eduardocasino/k-1008-visable-memory-card-replica/Address.kicad_sch

## KiCad design Address.kicad_sch (2023-08-17, an earlier design)

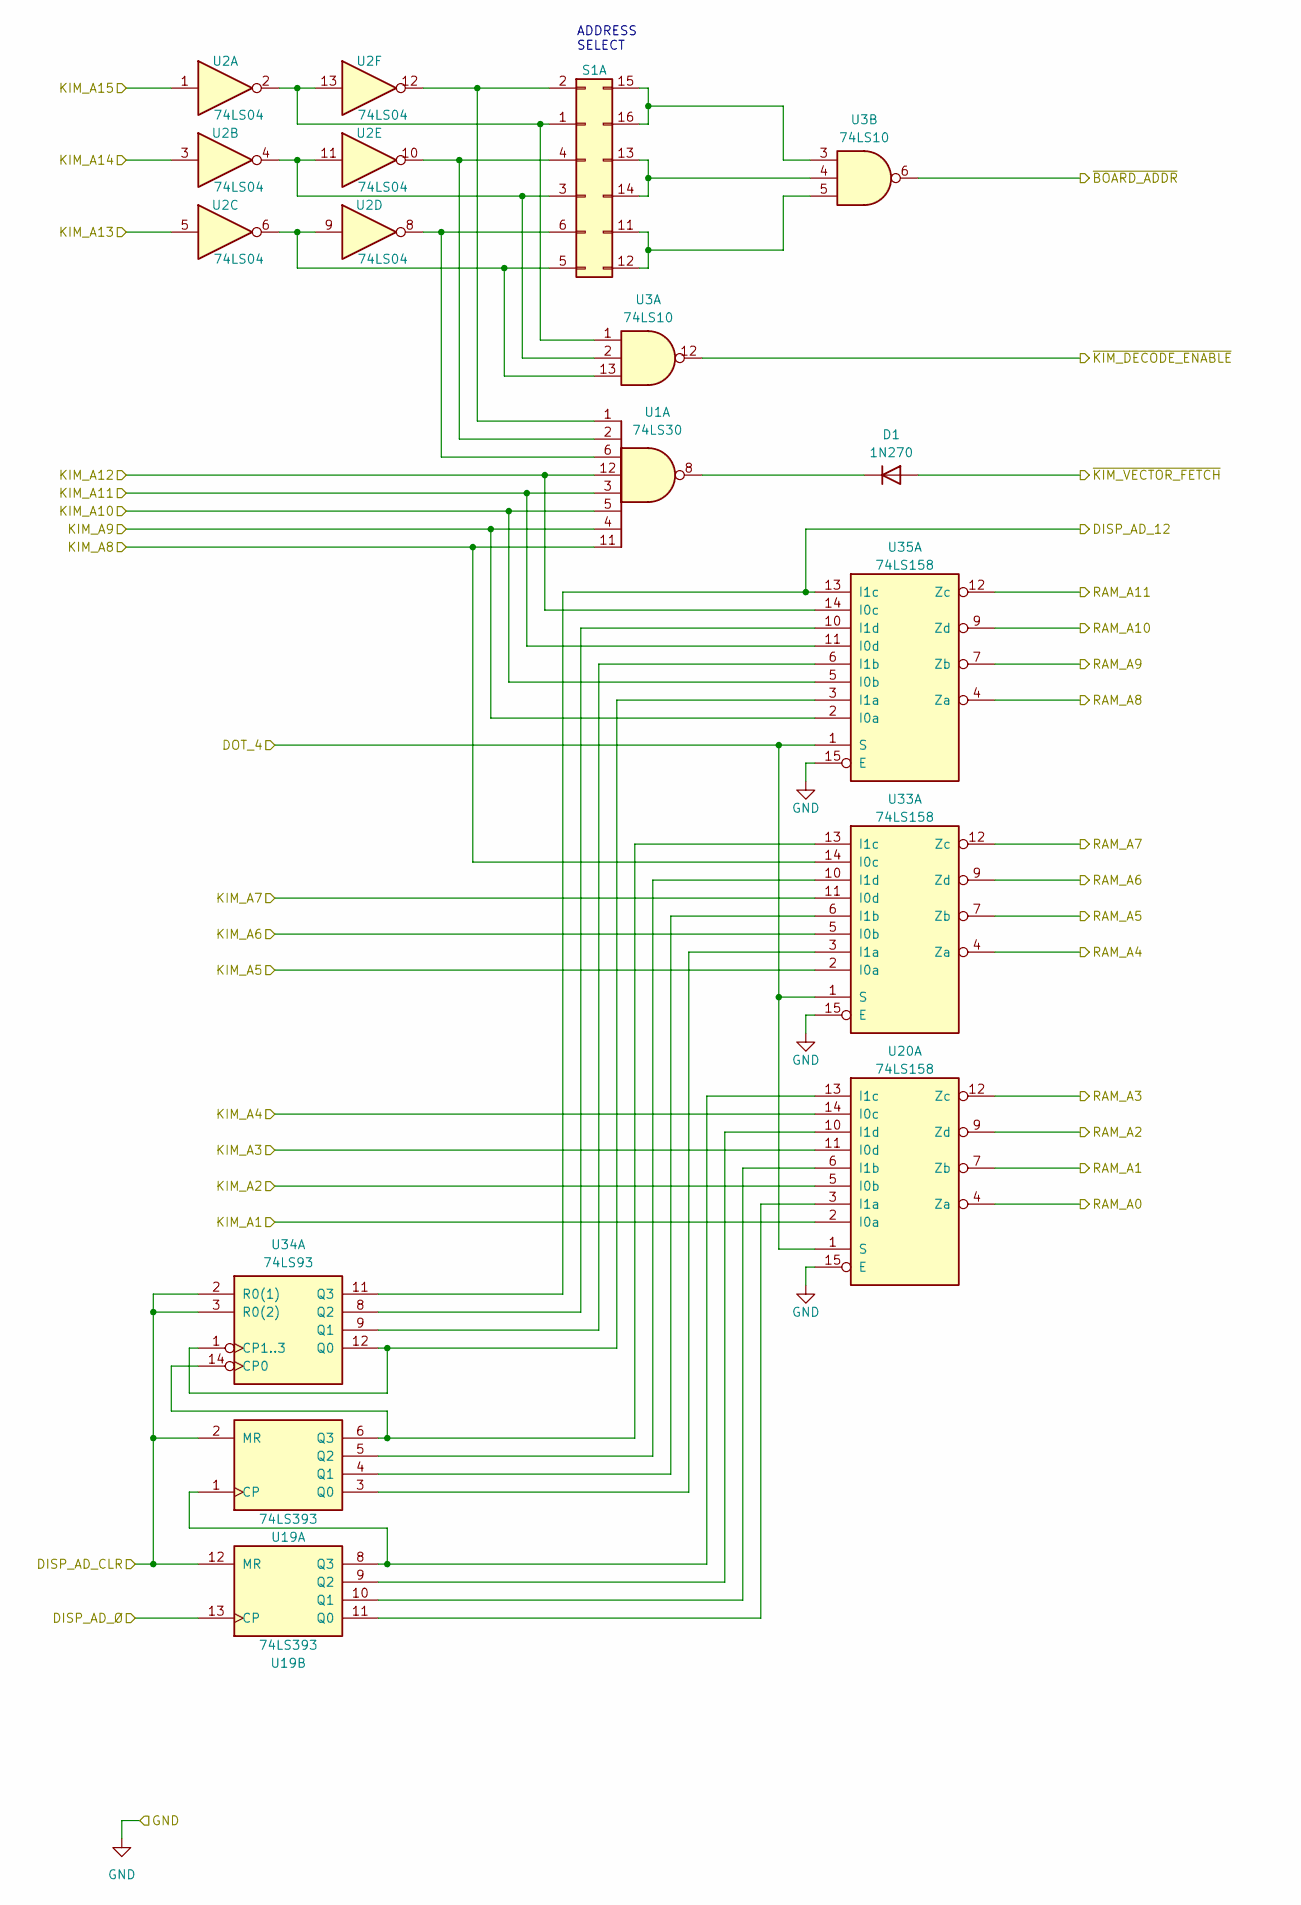
[picture p23: schematic Address.kicad_sch]

Parts:
D1: 1N270; D_DO-35_SOD27_P7.62mm_Horizontal
S1: DIP SOCKET FOR JUMPERS
U1: 74LS30
U2: 74LS04
U3: 74LS10
U19: 74LS393
U20, U33, U35: 74LS158
U34: 74LS93

Connections:
DISP_AD_12: U34.11 (Q3), U35.13 (I1c)
DISP_AD_CLR: U19.2 (MR), U19.12 (MR), U34.2 (R0(1)), U34.3 (R0(2))
DISP_AD_Ø: U19.13 (CP)
DOT_4: U20.1 (S), U33.1 (S), U35.1 (S)
GND: U20.15 (E), U33.15 (E), U35.15 (E)
KIM_A1: U20.2 (I0a)
KIM_A2: U20.5 (I0b)
KIM_A3: U20.11 (I0d)
KIM_A4: U20.14 (I0c)
KIM_A5: U33.2 (I0a)
KIM_A6: U33.5 (I0b)
KIM_A7: U33.11 (I0d)
KIM_A8: U1.11, U33.14 (I0c)
KIM_A9: U1.4, U35.2 (I0a)
KIM_A10: U1.5, U35.5 (I0b)
KIM_A11: U1.3, U35.11 (I0d)
KIM_A12: U1.12, U35.14 (I0c)
KIM_A13: U2.5
KIM_A14: U2.3
KIM_A15: U2.1
unnamed: D1.1 (K), U1.8
unnamed: S1.1, U2.2, U2.13, U3.1
unnamed: S1.2, U1.1, U2.12
unnamed: S1.3, U2.4, U2.11, U3.2
unnamed: S1.4, U1.2, U2.10
unnamed: S1.5, U2.6, U2.9, U3.13
unnamed: S1.6, U1.6, U2.8
unnamed: S1.11, S1.12, U3.5
unnamed: S1.13, S1.14, U3.4
unnamed: S1.15, S1.16, U3.3
unnamed: U19.1 (CP), U19.8 (Q3), U20.13 (I1c)
unnamed: U19.3 (Q0), U33.3 (I1a)
unnamed: U19.4 (Q1), U33.6 (I1b)
unnamed: U19.5 (Q2), U33.10 (I1d)
unnamed: U19.6 (Q3), U33.13 (I1c), U34.14 (CP0)
unnamed: U19.9 (Q2), U20.10 (I1d)
unnamed: U19.10 (Q1), U20.6 (I1b)
unnamed: U19.11 (Q0), U20.3 (I1a)
unnamed: U34.1 (CP1..3), U34.12 (Q0), U35.3 (I1a)
unnamed: U34.8 (Q2), U35.10 (I1d)
unnamed: U34.9 (Q1), U35.6 (I1b)
RAM_A0: U20.4 (Za)
RAM_A1: U20.7 (Zb)
RAM_A2: U20.9 (Zd)
RAM_A3: U20.12 (Zc)
RAM_A4: U33.4 (Za)
RAM_A5: U33.7 (Zb)
RAM_A6: U33.9 (Zd)
RAM_A7: U33.12 (Zc)
RAM_A8: U35.4 (Za)
RAM_A9: U35.7 (Zb)
RAM_A10: U35.9 (Zd)
RAM_A11: U35.12 (Zc)
~BOARD_ADDR: U3.6
~KIM_DECODE_ENABLE: U3.12
~KIM_VECTOR_FETCH: D1.2 (A)

Notes on the sheet:
ADDRESS SELECT
