eduardocasino/k-1008-visable-memory-card-replica/Power_pins_and_decoupling_caps.kicad_sch

## KiCad design Power_pins_and_decoupling_caps.kicad_sch (2023-08-17, an earlier design)

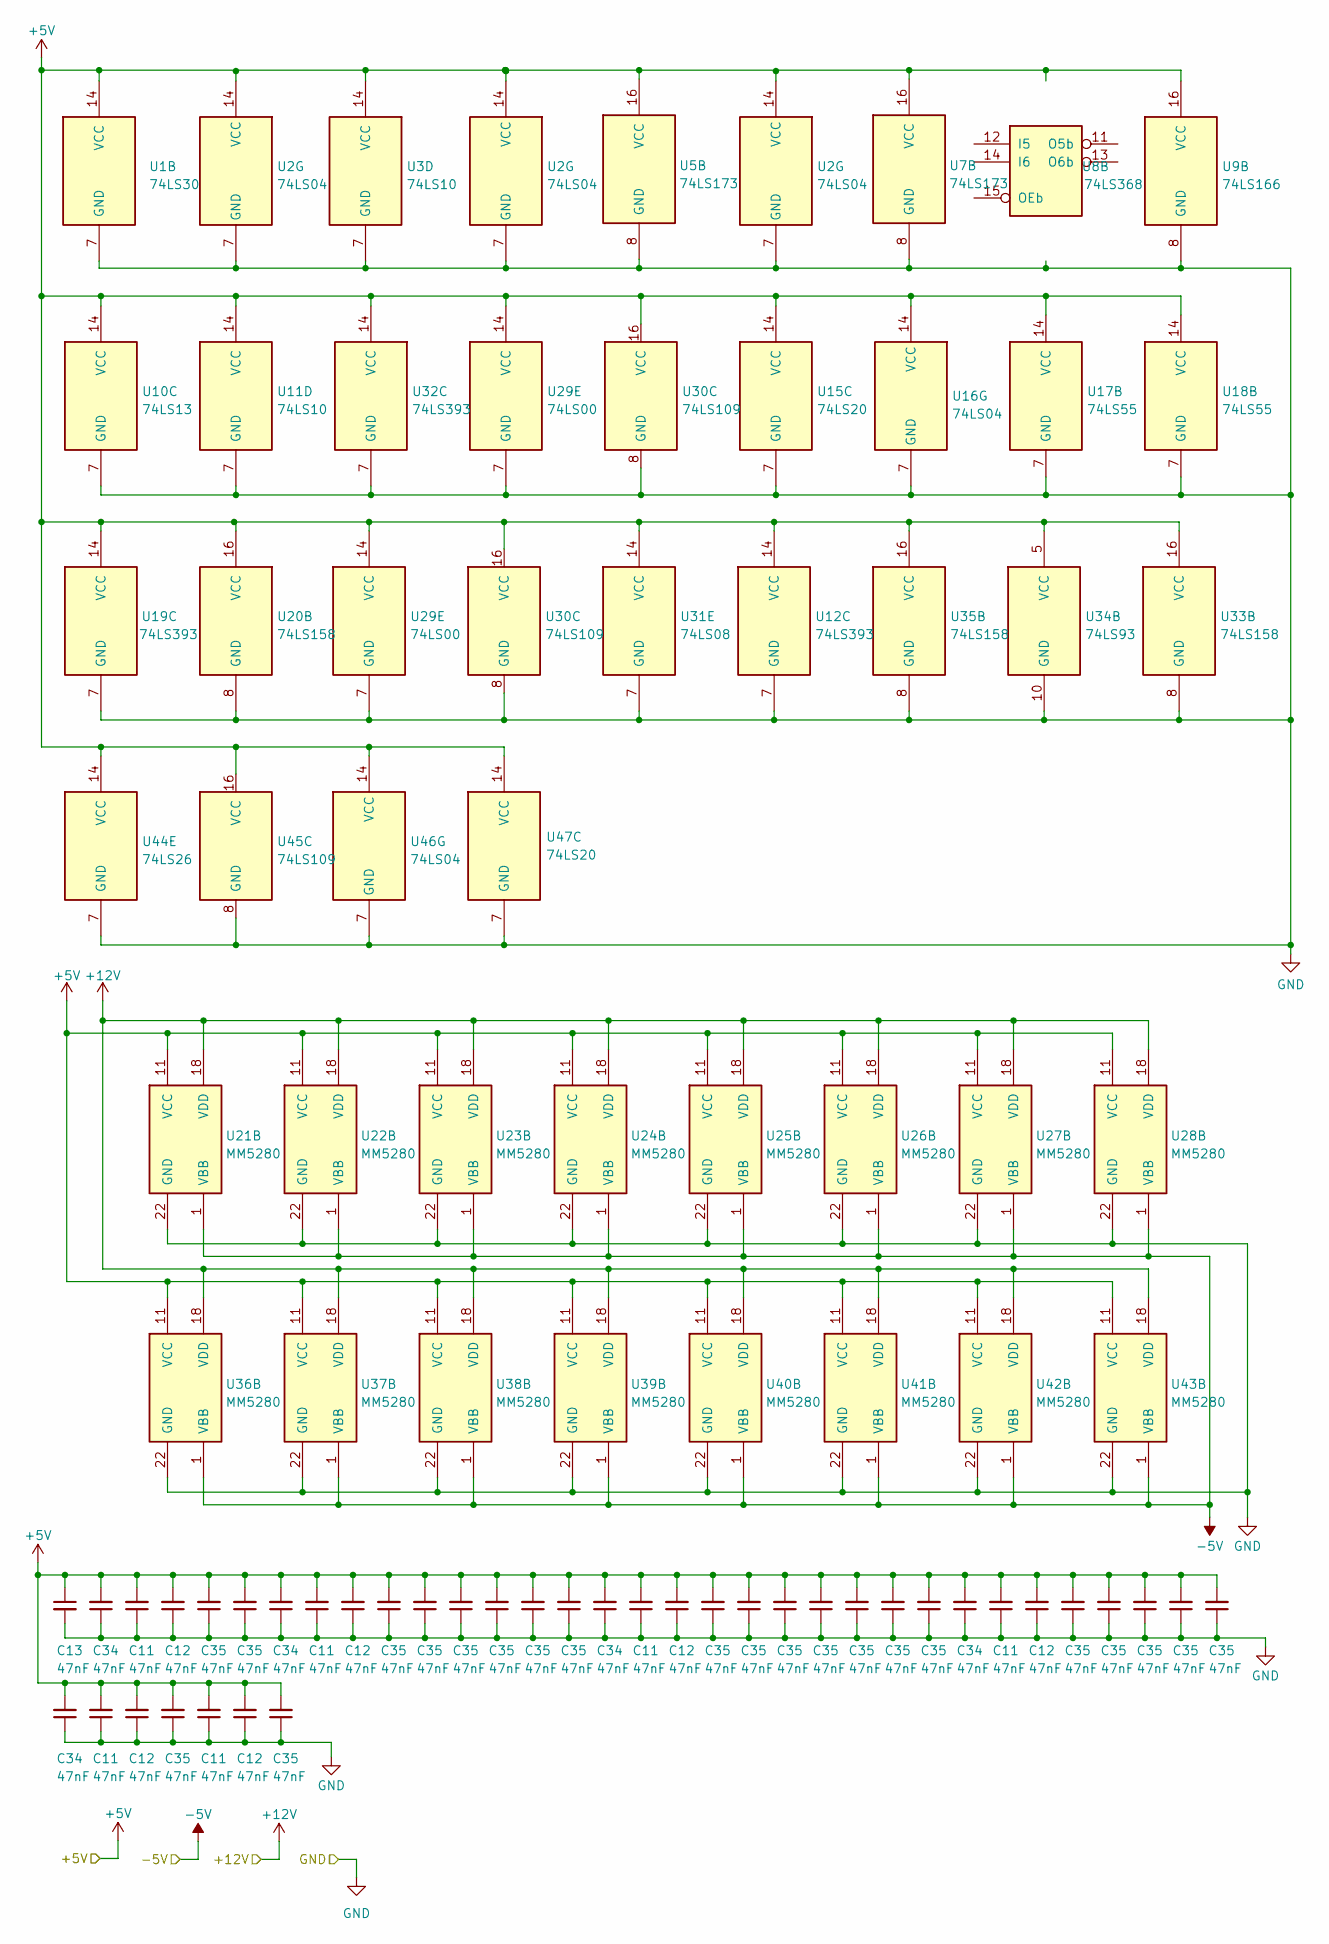
[picture p24: schematic Power_pins_and_decoupling_caps.kicad_sch]

Parts:
C11, C12, C13, C34, C35: 47nF
U1: 74LS30
U2, U16, U46: 74LS04
U3, U11: 74LS10
U5, U7: 74LS173
U8: 74LS368
U9: 74LS166
U10: 74LS13
U12, U19, U32: 74LS393
U15, U47: 74LS20
U17, U18: 74LS55
U20, U33, U35: 74LS158
U21, U22, U23, U24, U25, U26, U27, U28, U36, U37, U38, U39, U40, U41, U42, U43: MM5280
U29: 74LS00
U30, U45: 74LS109
U31: 74LS08
U34: 74LS93
U44: 74LS26

Connections:
+5V: C11.2, C12.2, C13.1, C34.2, C35.2, U1.14 (VCC), U2.14 (VCC), U3.14 (VCC), U5.16 (VCC), U7.16 (VCC), U9.16 (VCC), U10.14 (VCC), U11.14 (VCC), U12.14 (VCC), U15.14 (VCC), U16.14 (VCC), U17.14 (VCC), U18.14 (VCC), U19.14 (VCC), U20.16 (VCC), U21.11 (VCC), U22.11 (VCC), U23.11 (VCC), U24.11 (VCC), U25.11 (VCC), U26.11 (VCC), U27.11 (VCC), U28.11 (VCC), U29.14 (VCC), U30.16 (VCC), U31.14 (VCC), U32.14 (VCC), U33.16 (VCC), U34.5 (VCC), U35.16 (VCC), U36.11 (VCC), U37.11 (VCC), U38.11 (VCC), U39.11 (VCC), U40.11 (VCC), U41.11 (VCC), U42.11 (VCC), U43.11 (VCC), U44.14 (VCC), U45.16 (VCC), U46.14 (VCC), U47.14 (VCC)
+12V: U21.18 (VDD), U22.18 (VDD), U23.18 (VDD), U24.18 (VDD), U25.18 (VDD), U26.18 (VDD), U27.18 (VDD), U28.18 (VDD), U36.18 (VDD), U37.18 (VDD), U38.18 (VDD), U39.18 (VDD), U40.18 (VDD), U41.18 (VDD), U42.18 (VDD), U43.18 (VDD)
-5V: U21.1 (VBB), U22.1 (VBB), U23.1 (VBB), U24.1 (VBB), U25.1 (VBB), U26.1 (VBB), U27.1 (VBB), U28.1 (VBB), U36.1 (VBB), U37.1 (VBB), U38.1 (VBB), U39.1 (VBB), U40.1 (VBB), U41.1 (VBB), U42.1 (VBB), U43.1 (VBB)
GND: C11.1, C12.1, C13.2, C34.1, C35.1, U1.7 (GND), U2.7 (GND), U3.7 (GND), U5.8 (GND), U7.8 (GND), U9.8 (GND), U10.7 (GND), U11.7 (GND), U12.7 (GND), U15.7 (GND), U16.7 (GND), U17.7 (GND), U18.7 (GND), U19.7 (GND), U20.8 (GND), U21.22 (GND), U22.22 (GND), U23.22 (GND), U24.22 (GND), U25.22 (GND), U26.22 (GND), U27.22 (GND), U28.22 (GND), U29.7 (GND), U30.8 (GND), U31.7 (GND), U32.7 (GND), U33.8 (GND), U34.10 (GND), U35.8 (GND), U36.22 (GND), U37.22 (GND), U38.22 (GND), U39.22 (GND), U40.22 (GND), U41.22 (GND), U42.22 (GND), U43.22 (GND), U44.7 (GND), U45.8 (GND), U46.7 (GND), U47.7 (GND)
