eduardocasino/k-1008-visable-memory-card-replica/Ram_chips_high.kicad_sch

## KiCad design Ram_chips_high.kicad_sch (2023-07-14, an earlier design)

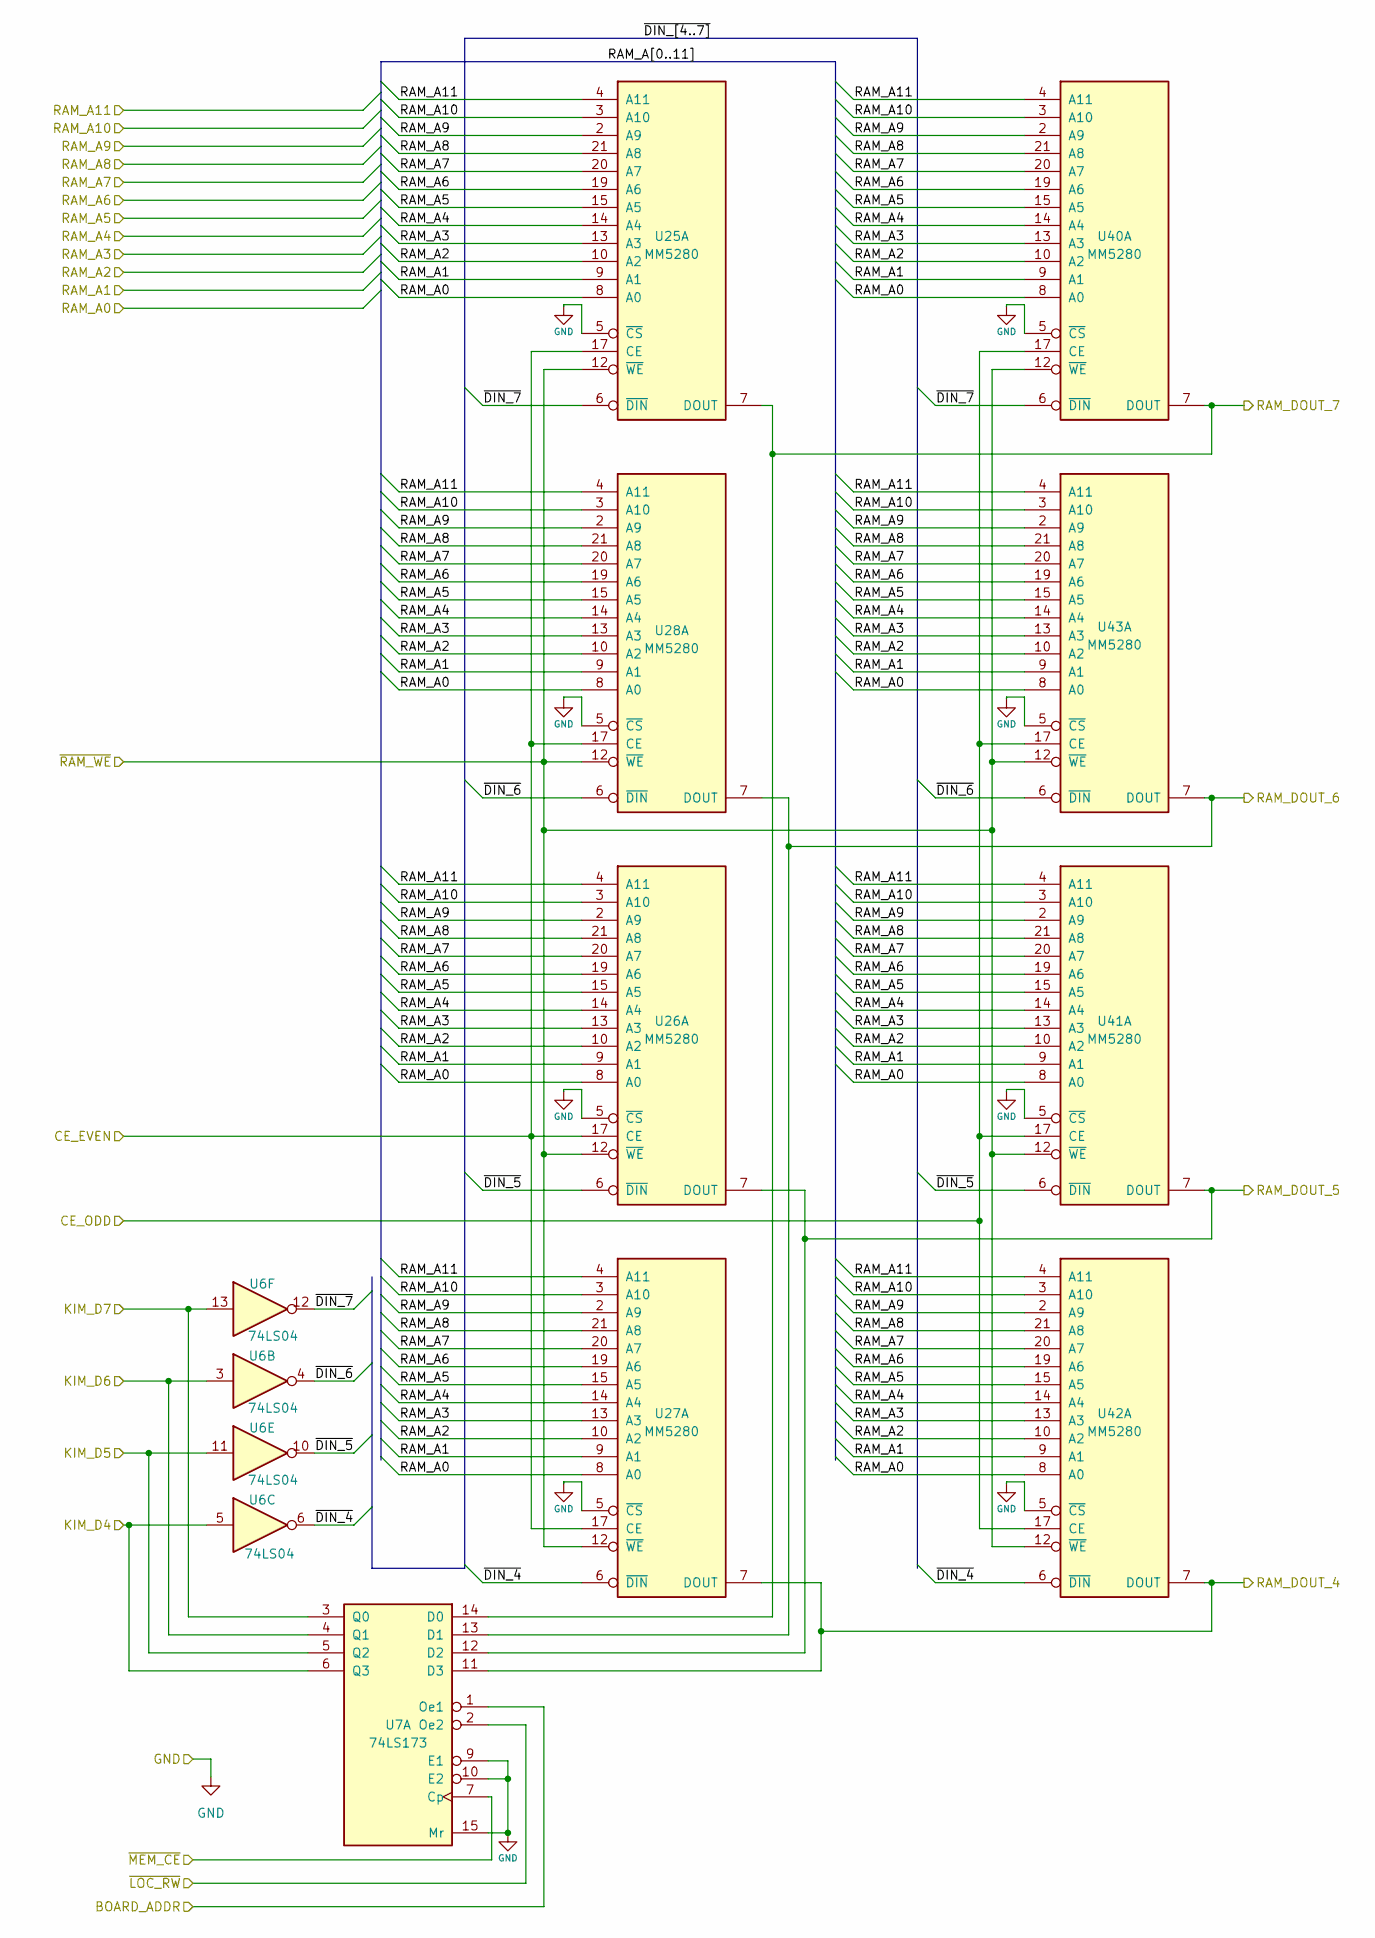
[picture p25: schematic Ram_chips_high.kicad_sch]

Parts:
U6: 74LS04
U7: 74LS173
U25, U26, U27, U28, U40, U41, U42, U43: MM5280

Connections:
BOARD_ADDR: U7.1 (Oe1)
CE_EVEN: U25.17 (CE), U26.17 (CE), U27.17 (CE), U28.17 (CE)
CE_ODD: U40.17 (CE), U41.17 (CE), U42.17 (CE), U43.17 (CE)
GND: U7.9 (E1), U7.10 (E2), U7.15 (Mr), U25.5 (~CS), U26.5 (~CS), U27.5 (~CS), U28.5 (~CS), U40.5 (~CS), U41.5 (~CS), U42.5 (~CS), U43.5 (~CS)
KIM_D4: U6.5, U7.6 (Q3)
KIM_D5: U6.11, U7.5 (Q2)
KIM_D6: U6.3, U7.4 (Q1)
KIM_D7: U6.13, U7.3 (Q0)
RAM_A0: U25.8 (A0), U26.8 (A0), U27.8 (A0), U28.8 (A0), U40.8 (A0), U41.8 (A0), U42.8 (A0), U43.8 (A0)
RAM_A1: U25.9 (A1), U26.9 (A1), U27.9 (A1), U28.9 (A1), U40.9 (A1), U41.9 (A1), U42.9 (A1), U43.9 (A1)
RAM_A2: U25.10 (A2), U26.10 (A2), U27.10 (A2), U28.10 (A2), U40.10 (A2), U41.10 (A2), U42.10 (A2), U43.10 (A2)
RAM_A3: U25.13 (A3), U26.13 (A3), U27.13 (A3), U28.13 (A3), U40.13 (A3), U41.13 (A3), U42.13 (A3), U43.13 (A3)
RAM_A4: U25.14 (A4), U26.14 (A4), U27.14 (A4), U28.14 (A4), U40.14 (A4), U41.14 (A4), U42.14 (A4), U43.14 (A4)
RAM_A5: U25.15 (A5), U26.15 (A5), U27.15 (A5), U28.15 (A5), U40.15 (A5), U41.15 (A5), U42.15 (A5), U43.15 (A5)
RAM_A6: U25.19 (A6), U26.19 (A6), U27.19 (A6), U28.19 (A6), U40.19 (A6), U41.19 (A6), U42.19 (A6), U43.19 (A6)
RAM_A7: U25.20 (A7), U26.20 (A7), U27.20 (A7), U28.20 (A7), U40.20 (A7), U41.20 (A7), U42.20 (A7), U43.20 (A7)
RAM_A8: U25.21 (A8), U26.21 (A8), U27.21 (A8), U28.21 (A8), U40.21 (A8), U41.21 (A8), U42.21 (A8), U43.21 (A8)
RAM_A9: U25.2 (A9), U26.2 (A9), U27.2 (A9), U28.2 (A9), U40.2 (A9), U41.2 (A9), U42.2 (A9), U43.2 (A9)
RAM_A10: U25.3 (A10), U26.3 (A10), U27.3 (A10), U28.3 (A10), U40.3 (A10), U41.3 (A10), U42.3 (A10), U43.3 (A10)
RAM_A11: U25.4 (A11), U26.4 (A11), U27.4 (A11), U28.4 (A11), U40.4 (A11), U41.4 (A11), U42.4 (A11), U43.4 (A11)
RAM_DOUT_4: U7.11 (D3), U27.7 (DOUT), U42.7 (DOUT)
RAM_DOUT_5: U7.12 (D2), U26.7 (DOUT), U41.7 (DOUT)
RAM_DOUT_6: U7.13 (D1), U28.7 (DOUT), U43.7 (DOUT)
RAM_DOUT_7: U7.14 (D0), U25.7 (DOUT), U40.7 (DOUT)
~DIN_4: U6.6, U27.6 (~DIN), U42.6 (~DIN)
~DIN_5: U6.10, U26.6 (~DIN), U41.6 (~DIN)
~DIN_6: U6.4, U28.6 (~DIN), U43.6 (~DIN)
~DIN_7: U6.12, U25.6 (~DIN), U40.6 (~DIN)
~LOC_RW: U7.2 (Oe2)
~MEM_CE: U7.7 (Cp)
~RAM_WE: U25.12 (~WE), U26.12 (~WE), U27.12 (~WE), U28.12 (~WE), U40.12 (~WE), U41.12 (~WE), U42.12 (~WE), U43.12 (~WE)
