eduardocasino/k-1008-visable-memory-card-replica/Sync_and_video.kicad_sch

## KiCad design Sync_and_video.kicad_sch (2023-08-01, an earlier design)

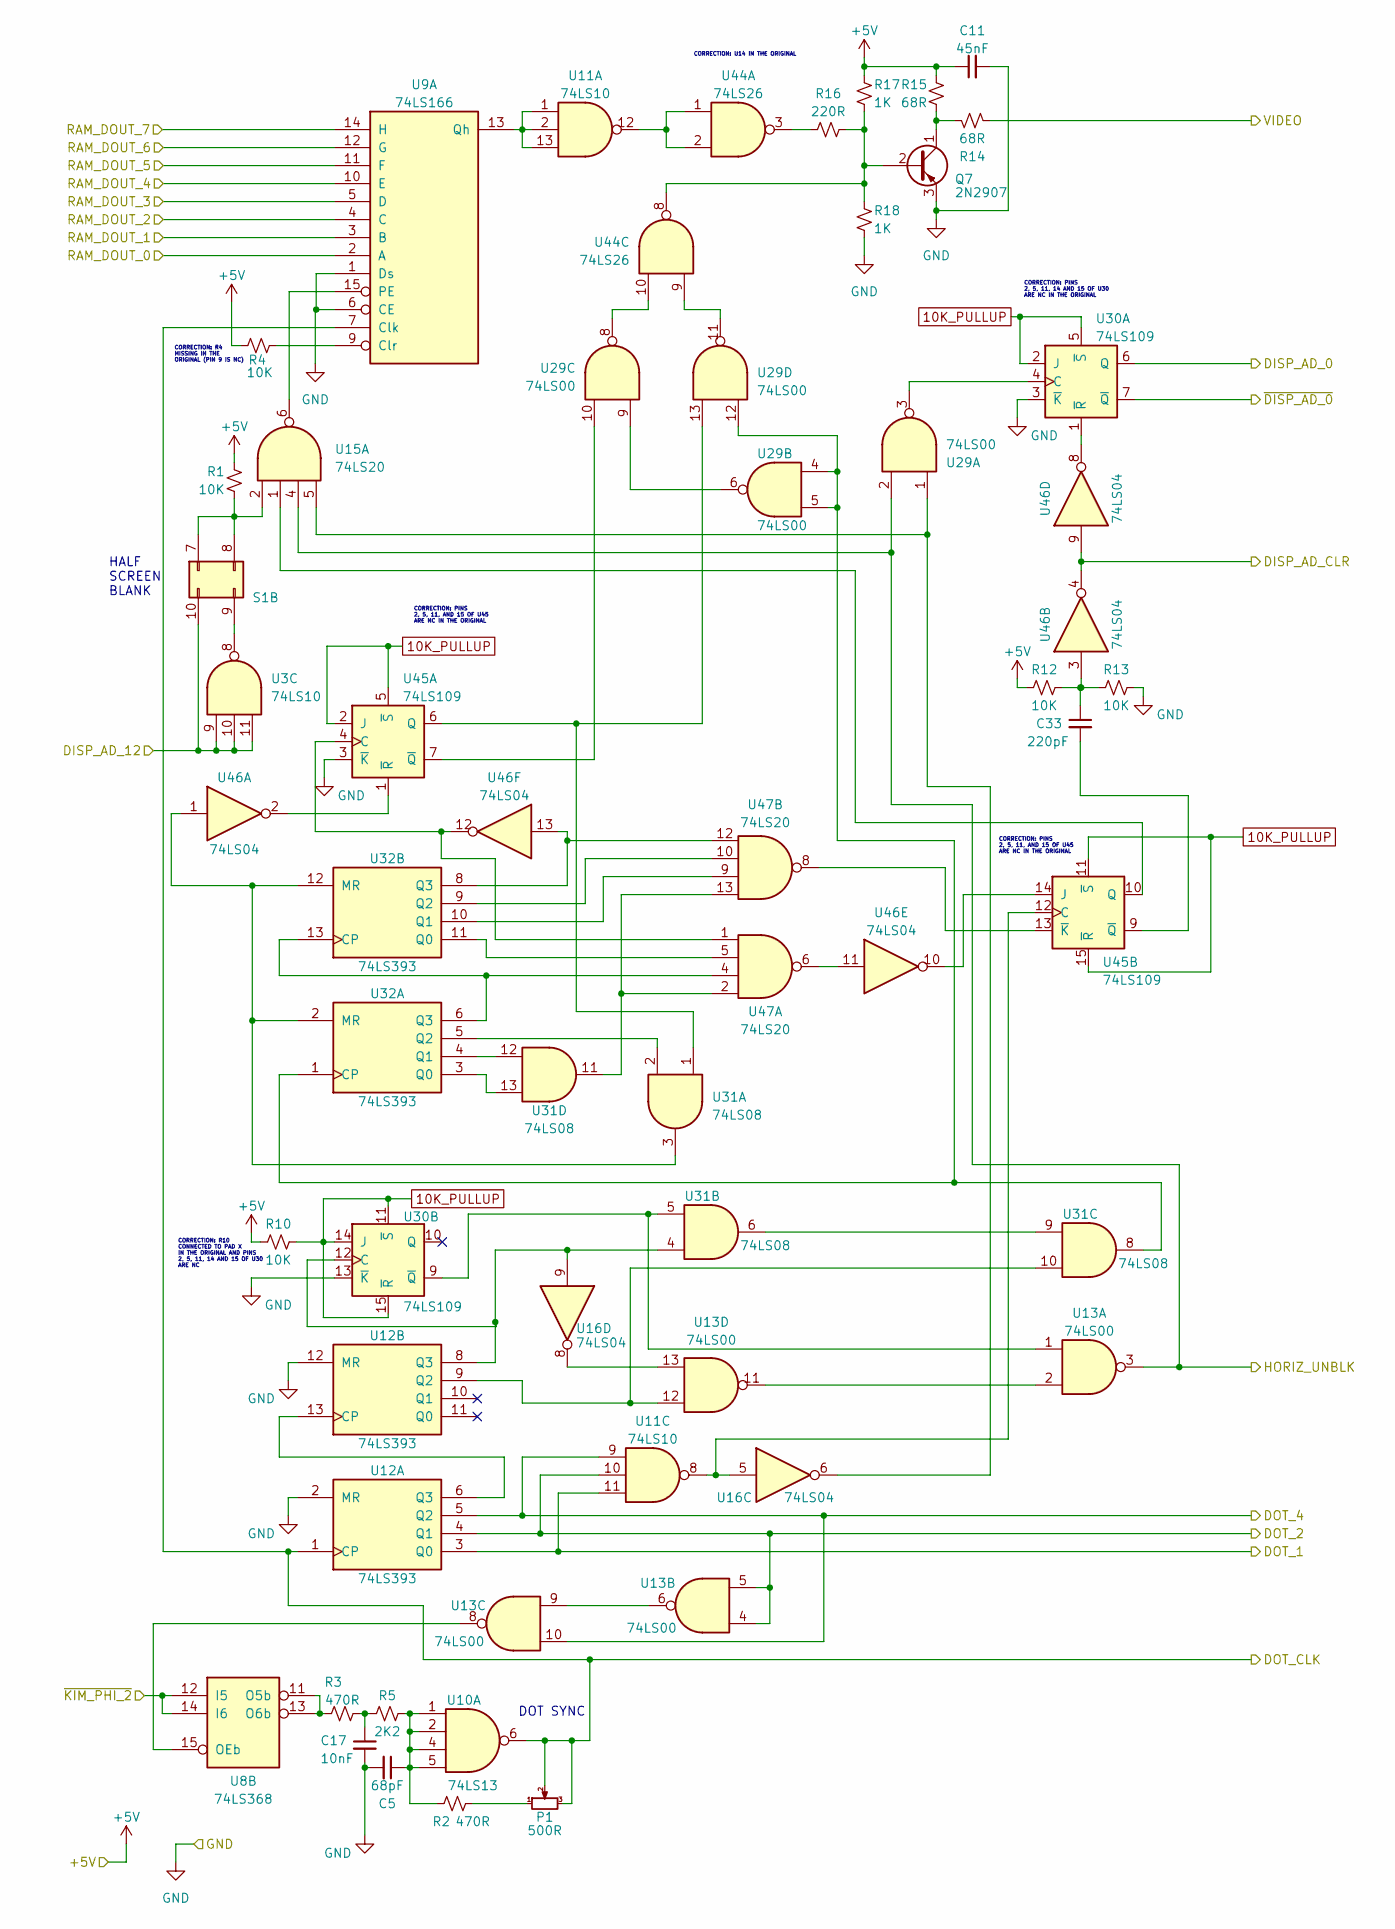
[picture p26: schematic Sync_and_video.kicad_sch]

Parts:
C5: 68pF
C11: 45nF
C17: 10nF
C33: 220pF
P1: 500R
Q7: 2N2907; TO-92_Inline
R1, R4, R10, R12, R13: 10K
R2, R3: 470R
R5: 2K2
R14, R15: 68R
R16: 220R
R17, R18: 1K
S1: DIP SOCKET FOR JUMPERS
U3, U11: 74LS10
U8: 74LS368
U9: 74LS166
U10: 74LS13
U12, U32: 74LS393
U13, U29: 74LS00
U15, U47: 74LS20
U16, U46: 74LS04
U30, U45: 74LS109
U31: 74LS08
U44: 74LS26

Connections:
10K_PULLUP: R10.2, U30.2 (J), U30.5 (~S), U30.11 (~S), U30.14 (J), U30.15 (~R), U45.2 (J), U45.5 (~S), U45.11 (~S), U45.15 (~R)
+5V: C11.1, R1.2, R4.2, R10.1, R12.1, R15.2, R17.2
DISP_AD_0: U30.6 (Q)
DISP_AD_12: S1.10, U3.9, U3.10, U3.11
DISP_AD_CLR: U46.4, U46.9
DOT_1: U11.11, U12.3 (Q0)
DOT_2: U11.10, U12.4 (Q1), U13.4, U13.5
DOT_4: U11.9, U12.5 (Q2), U13.10
DOT_CLK: P1.2, P1.3, U9.7 (Clk), U10.6, U12.1 (CP)
GND: C5.2, C11.2, C17.2, Q7.3 (E), R13.2, R18.1, U9.1 (Ds), U9.6 (CE), U12.2 (MR), U12.12 (MR), U30.3 (~K), U30.13 (~K), U45.3 (~K)
HORIZ_UNBLK: U13.3, U15.4, U29.2
unnamed: C5.1, R2.1, R5.2, U10.1, U10.2, U10.4, U10.5
unnamed: C17.1, R3.2, R5.1
unnamed: C33.1, R12.2, R13.1, U46.3
unnamed: C33.2, U45.9 (~Q)
unnamed: P1.1, R2.2
unnamed: Q7.1 (C), R14.1, R15.1
unnamed: Q7.2 (B), R16.2, R17.1, R18.2, U44.8
unnamed: R1.1, S1.7, S1.8, U15.2
unnamed: R3.1, U8.11 (O5b), U8.13 (O6b)
unnamed: R4.1, U9.9 (Clr)
unnamed: R16.1, U44.3
unnamed: S1.9, U3.8
unnamed: U9.13 (Qh), U11.1, U11.2, U11.13
unnamed: U11.8, U16.5, U45.12 (C)
unnamed: U11.12, U44.1, U44.2
unnamed: U12.8 (Q3), U16.9, U30.12 (C), U31.4
unnamed: U12.9 (Q2), U13.12, U31.10
unnamed: U12.6 (Q3), U12.13 (CP)
unnamed: U13.1, U30.9 (~Q), U31.5
unnamed: U13.6, U13.9
unnamed: U8.15 (OEb), U13.8
unnamed: U13.2, U13.11
unnamed: U13.13, U16.8
unnamed: U15.1, U45.10 (Q)
unnamed: U15.5, U16.6, U29.1
unnamed: U9.15 (PE), U15.6
unnamed: U29.3, U30.4 (C)
unnamed: U29.6, U29.9
unnamed: U29.8, U44.10
unnamed: U29.10, U45.7 (~Q)
unnamed: U29.11, U44.9
unnamed: U29.4, U29.5, U29.12, U31.8, U32.1 (CP)
unnamed: U29.13, U31.1, U45.6 (Q)
unnamed: U30.1 (~R), U46.8
unnamed: U31.2, U32.5 (Q2)
unnamed: U31.3, U32.2 (MR), U32.12 (MR), U46.1
unnamed: U31.6, U31.9
unnamed: U31.11, U47.2, U47.13
unnamed: U31.12, U32.4 (Q1)
unnamed: U31.13, U32.3 (Q0)
unnamed: U32.8 (Q3), U46.13, U47.12
unnamed: U32.9 (Q2), U47.10
unnamed: U32.10 (Q1), U47.9
unnamed: U32.11 (Q0), U47.5
unnamed: U32.6 (Q3), U32.13 (CP), U47.4
unnamed: U45.1 (~R), U46.2
unnamed: U45.4 (C), U46.12, U47.1
unnamed: U45.13 (~K), U47.8
unnamed: U45.14 (J), U46.10
unnamed: U46.11, U47.6
RAM_DOUT_0: U9.2 (A)
RAM_DOUT_1: U9.3 (B)
RAM_DOUT_2: U9.4 (C)
RAM_DOUT_3: U9.5 (D)
RAM_DOUT_4: U9.10 (E)
RAM_DOUT_5: U9.11 (F)
RAM_DOUT_6: U9.12 (G)
RAM_DOUT_7: U9.14 (H)
VIDEO: R14.2
~DISP_AD_0: U30.7 (~Q)
~KIM_PHI_2: U8.12 (I5), U8.14 (I6)

Notes on the sheet:
CORRECTION: U14 IN THE ORIGINAL
CORRECTION: PINS 2, 5, 11, AND 15 OF U45 ARE NC IN THE ORIGINAL
CORRECTION: PINS 2, 5, 11, 14 AND 15 OF U30 ARE NC IN THE ORIGINAL
DOT SYNC
CORRECTION: R10 CONNECTED TO PAD X IN THE ORIGINAL AND PINS 2, 5, 11, 14 AND 15 OF U30 ARE NC
HALF SCREEN BLANK
CORRECTION: R4 MISSING IN THE ORIGINAL (PIN 9 IS NC)
