eduardocasino/k-1008-visable-memory-card-replica/Timing_gen_and_power_supply.kicad_sch

## KiCad design Timing_gen_and_power_supply.kicad_sch (2023-08-17, an earlier design)

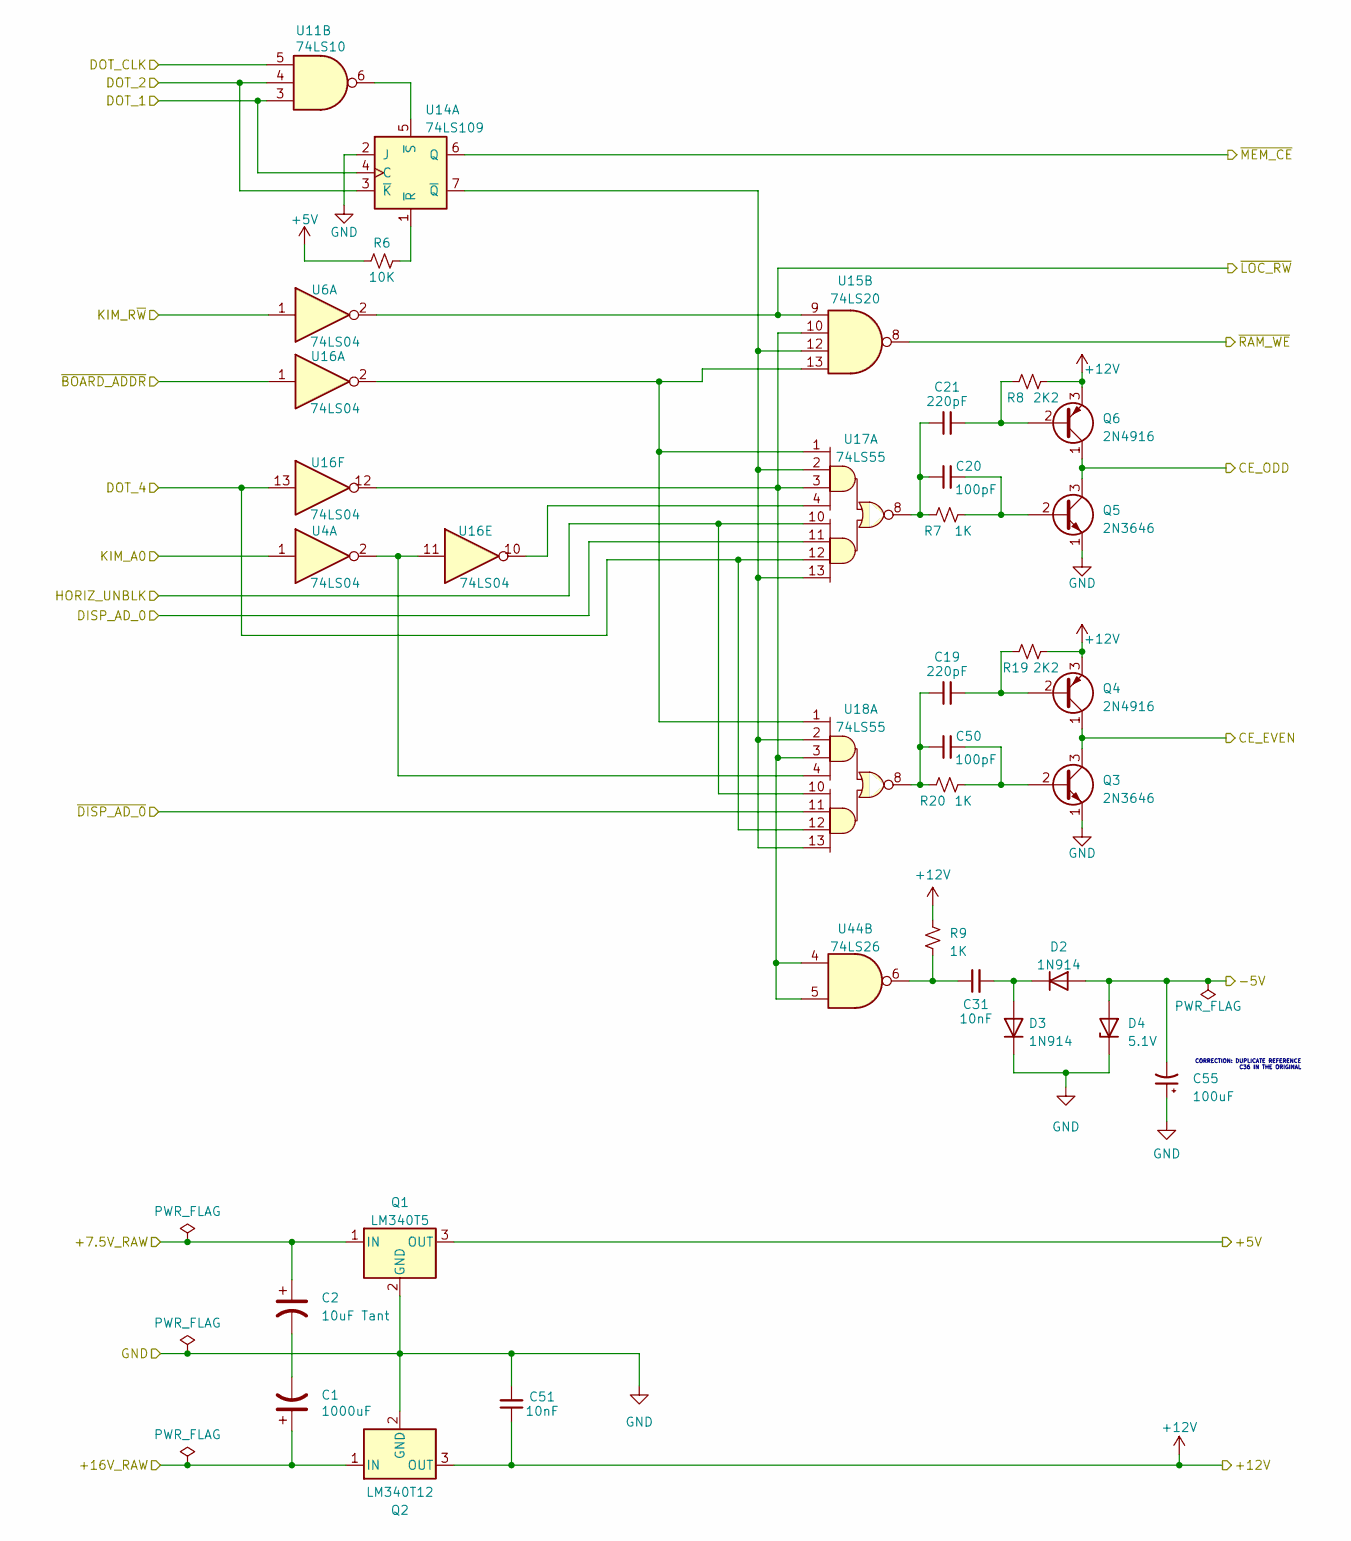
[picture p27: schematic Timing_gen_and_power_supply.kicad_sch]

Parts:
C1: 1000uF
C2: 10uF Tant
C19, C21: 220pF
C20, C50: 100pF
C31, C51: 10nF
C55: 100uF
D2, D3: 1N914; D_DO-35_SOD27_P7.62mm_Horizontal
D4: 5.1V
Q1: LM340T5
Q2: LM340T12
Q3, Q5: 2N3646; TO-92_Inline
Q4, Q6: 2N4916; TO-92_Inline
R6: 10K
R7, R9, R20: 1K
R8, R19: 2K2
U4, U6, U16: 74LS04
U11: 74LS10
U14: 74LS109
U15: 74LS20
U17, U18: 74LS55
U44: 74LS26

Connections:
+5V: Q1.3 (OUT), R6.1
+7.5V_RAW: C2.1, Q1.1 (IN)
+12V: C51.1, Q2.3 (OUT), Q4.3 (E), Q6.3 (E), R8.1, R9.1, R19.1
+16V_RAW: C1.1, Q2.1 (IN)
-5V: C55.2, D2.2 (A), D4.2 (A)
CE_EVEN: Q3.3 (C), Q4.1 (C)
CE_ODD: Q5.3 (C), Q6.1 (C)
DISP_AD_0: U17.11
DOT_1: U11.3, U14.4 (C)
DOT_2: U11.4, U14.3 (~K)
DOT_4: U16.13, U17.12, U18.12
DOT_CLK: U11.5
GND: C51.2, C55.1, D3.1 (K), D4.1 (K), Q1.2 (GND), Q2.2 (GND), Q3.1 (E), Q5.1 (E), U14.2 (J)
HORIZ_UNBLK: U17.10, U18.10
KIM_A0: U4.1
KIM_R~W: U6.1
unnamed: C1.2, C2.2
unnamed: C19.1, C50.1, R20.2, U18.8
unnamed: C19.2, Q4.2 (B), R19.2
unnamed: C20.1, C21.1, R7.2, U17.8
unnamed: C20.2, Q5.2 (B), R7.1
unnamed: C21.2, Q6.2 (B), R8.2
unnamed: C31.1, R9.2, U44.6
unnamed: C31.2, D2.1 (K), D3.2 (A)
unnamed: C50.2, Q3.2 (B), R20.1
unnamed: R6.2, U14.1 (~R)
unnamed: U11.6, U14.5 (~S)
unnamed: U14.7 (~Q), U15.12, U17.2, U17.13, U18.2, U18.13
unnamed: U15.10, U16.12, U17.3, U18.3, U44.4, U44.5
unnamed: U15.13, U16.2, U17.1, U18.1
unnamed: U16.10, U17.4
unnamed: U4.2, U16.11, U18.4
~BOARD_ADDR: U16.1
~DISP_AD_0: U18.11
~LOC_RW: U6.2, U15.9
~MEM_CE: U14.6 (Q)
~RAM_WE: U15.8

Notes on the sheet:
CORRECTION: DUPLICATE REFERENCE C36 IN THE ORIGINAL
