eduardocasino/k-1008-visable-memory-card-replica/Unused_units.kicad_sch

## KiCad design Unused_units.kicad_sch (2023-07-14, an earlier design)

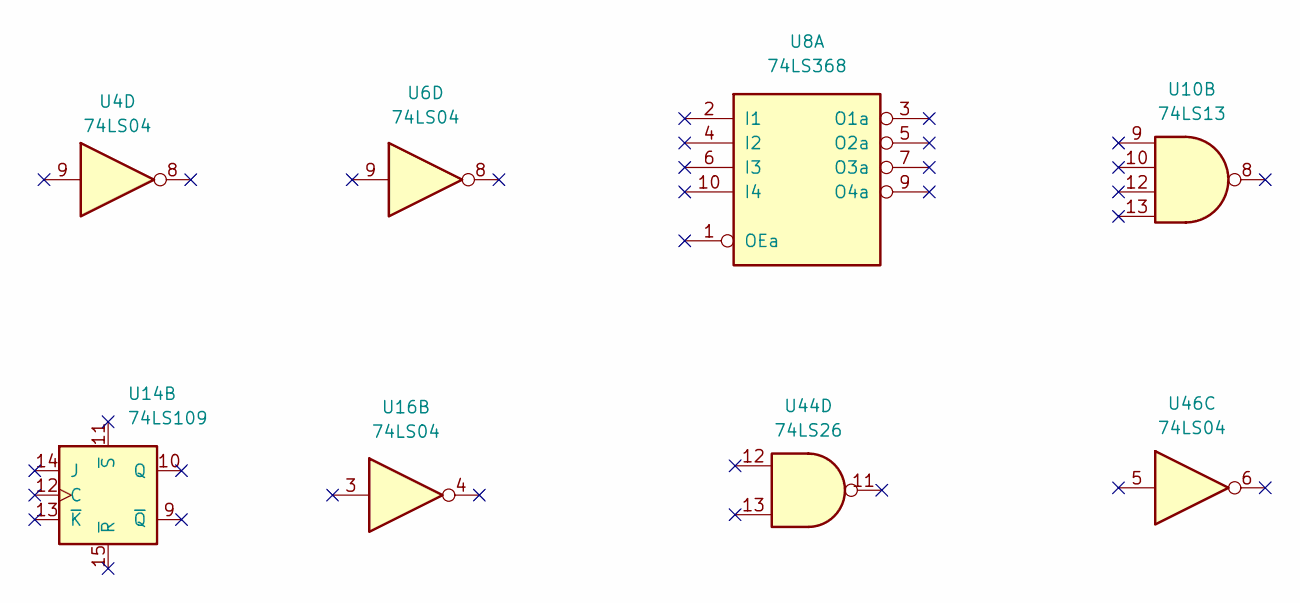
[picture p28: schematic Unused_units.kicad_sch]

Parts:
U4, U6, U16, U46: 74LS04
U8: 74LS368
U10: 74LS13
U14: 74LS109
U44: 74LS26
