eduardocasino/k-1008-visable-memory-card-replica/k-1008-visable-memory.kicad_sch

## KiCad design k-1008-visable-memory.kicad_sch (2023-07-03, an earlier design)

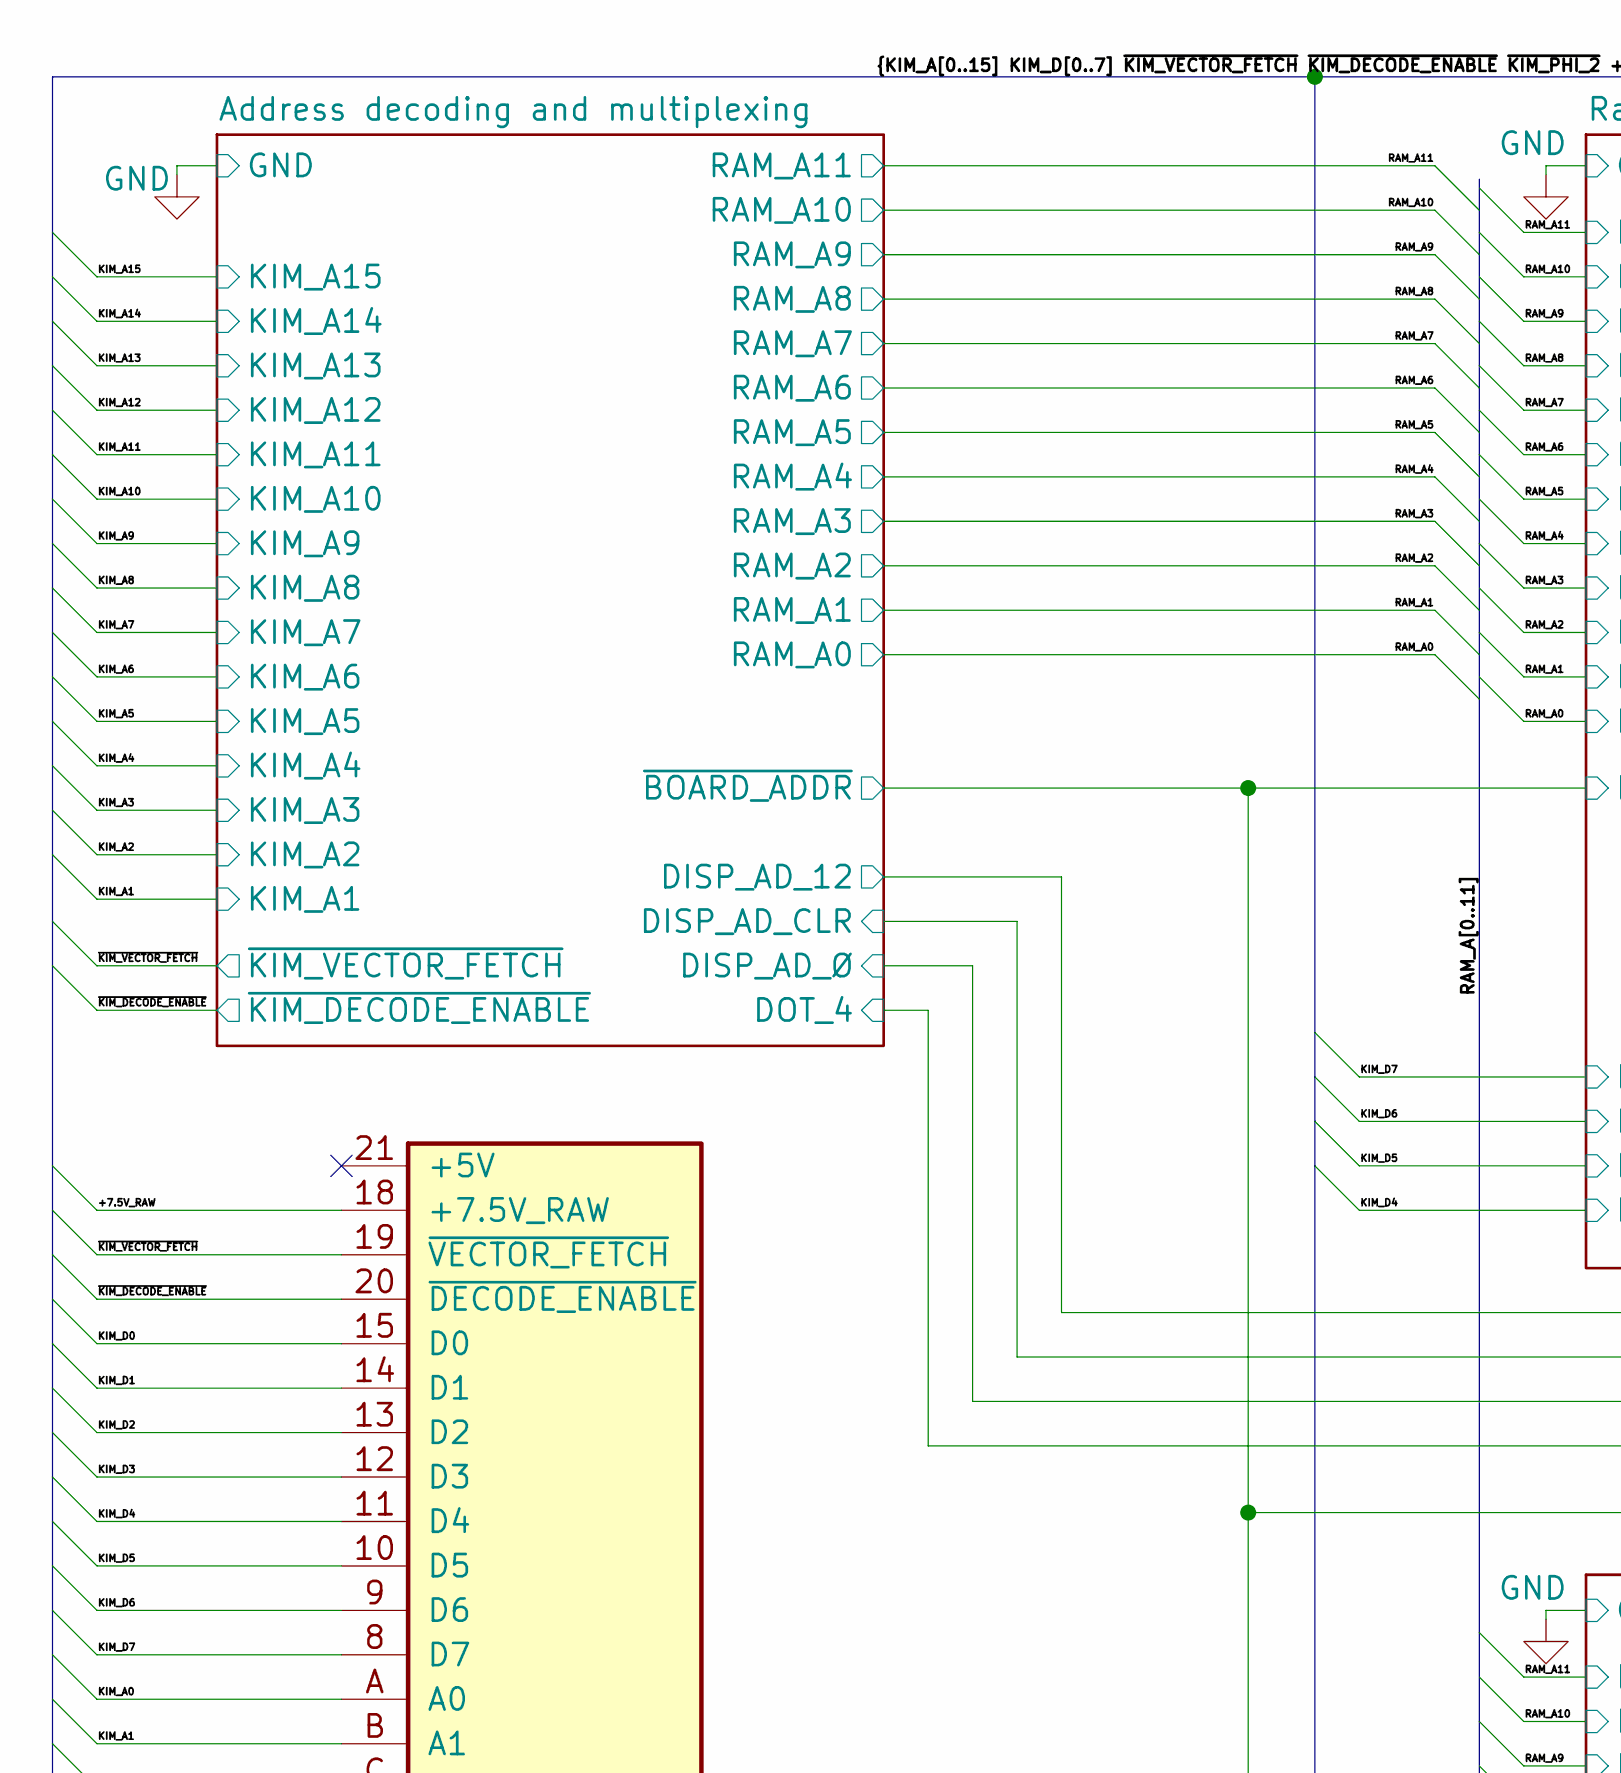
[picture p29: schematic k-1008-visable-memory.kicad_sch, part in row 1, column 1]

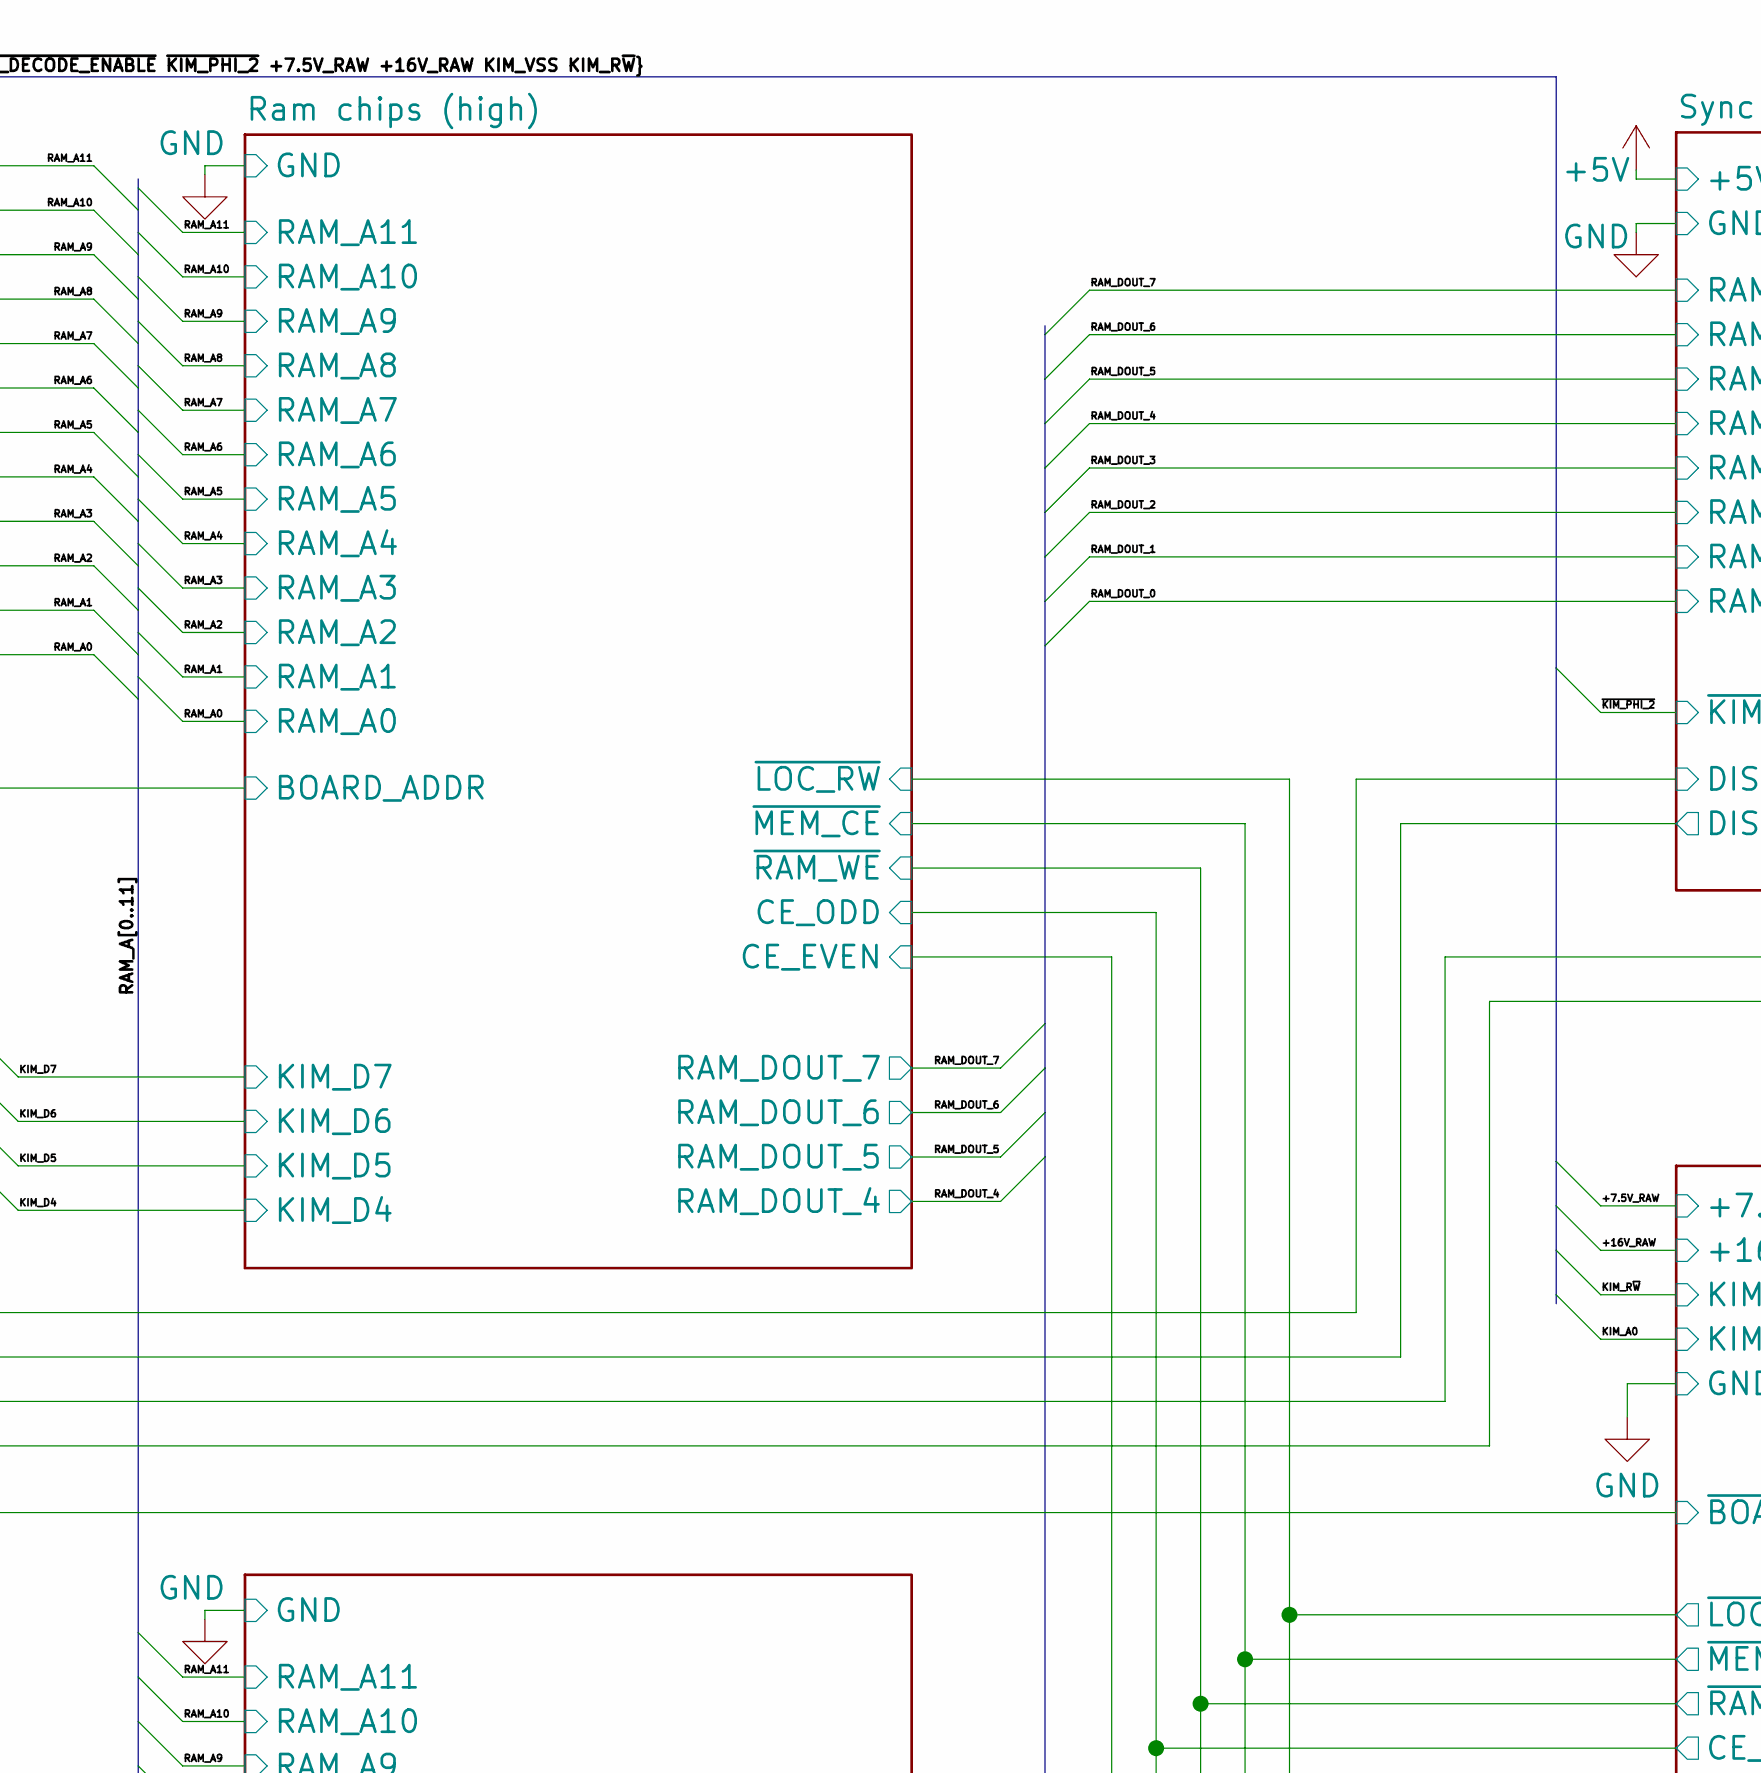
[picture p30: schematic k-1008-visable-memory.kicad_sch, part in row 1, column 2]

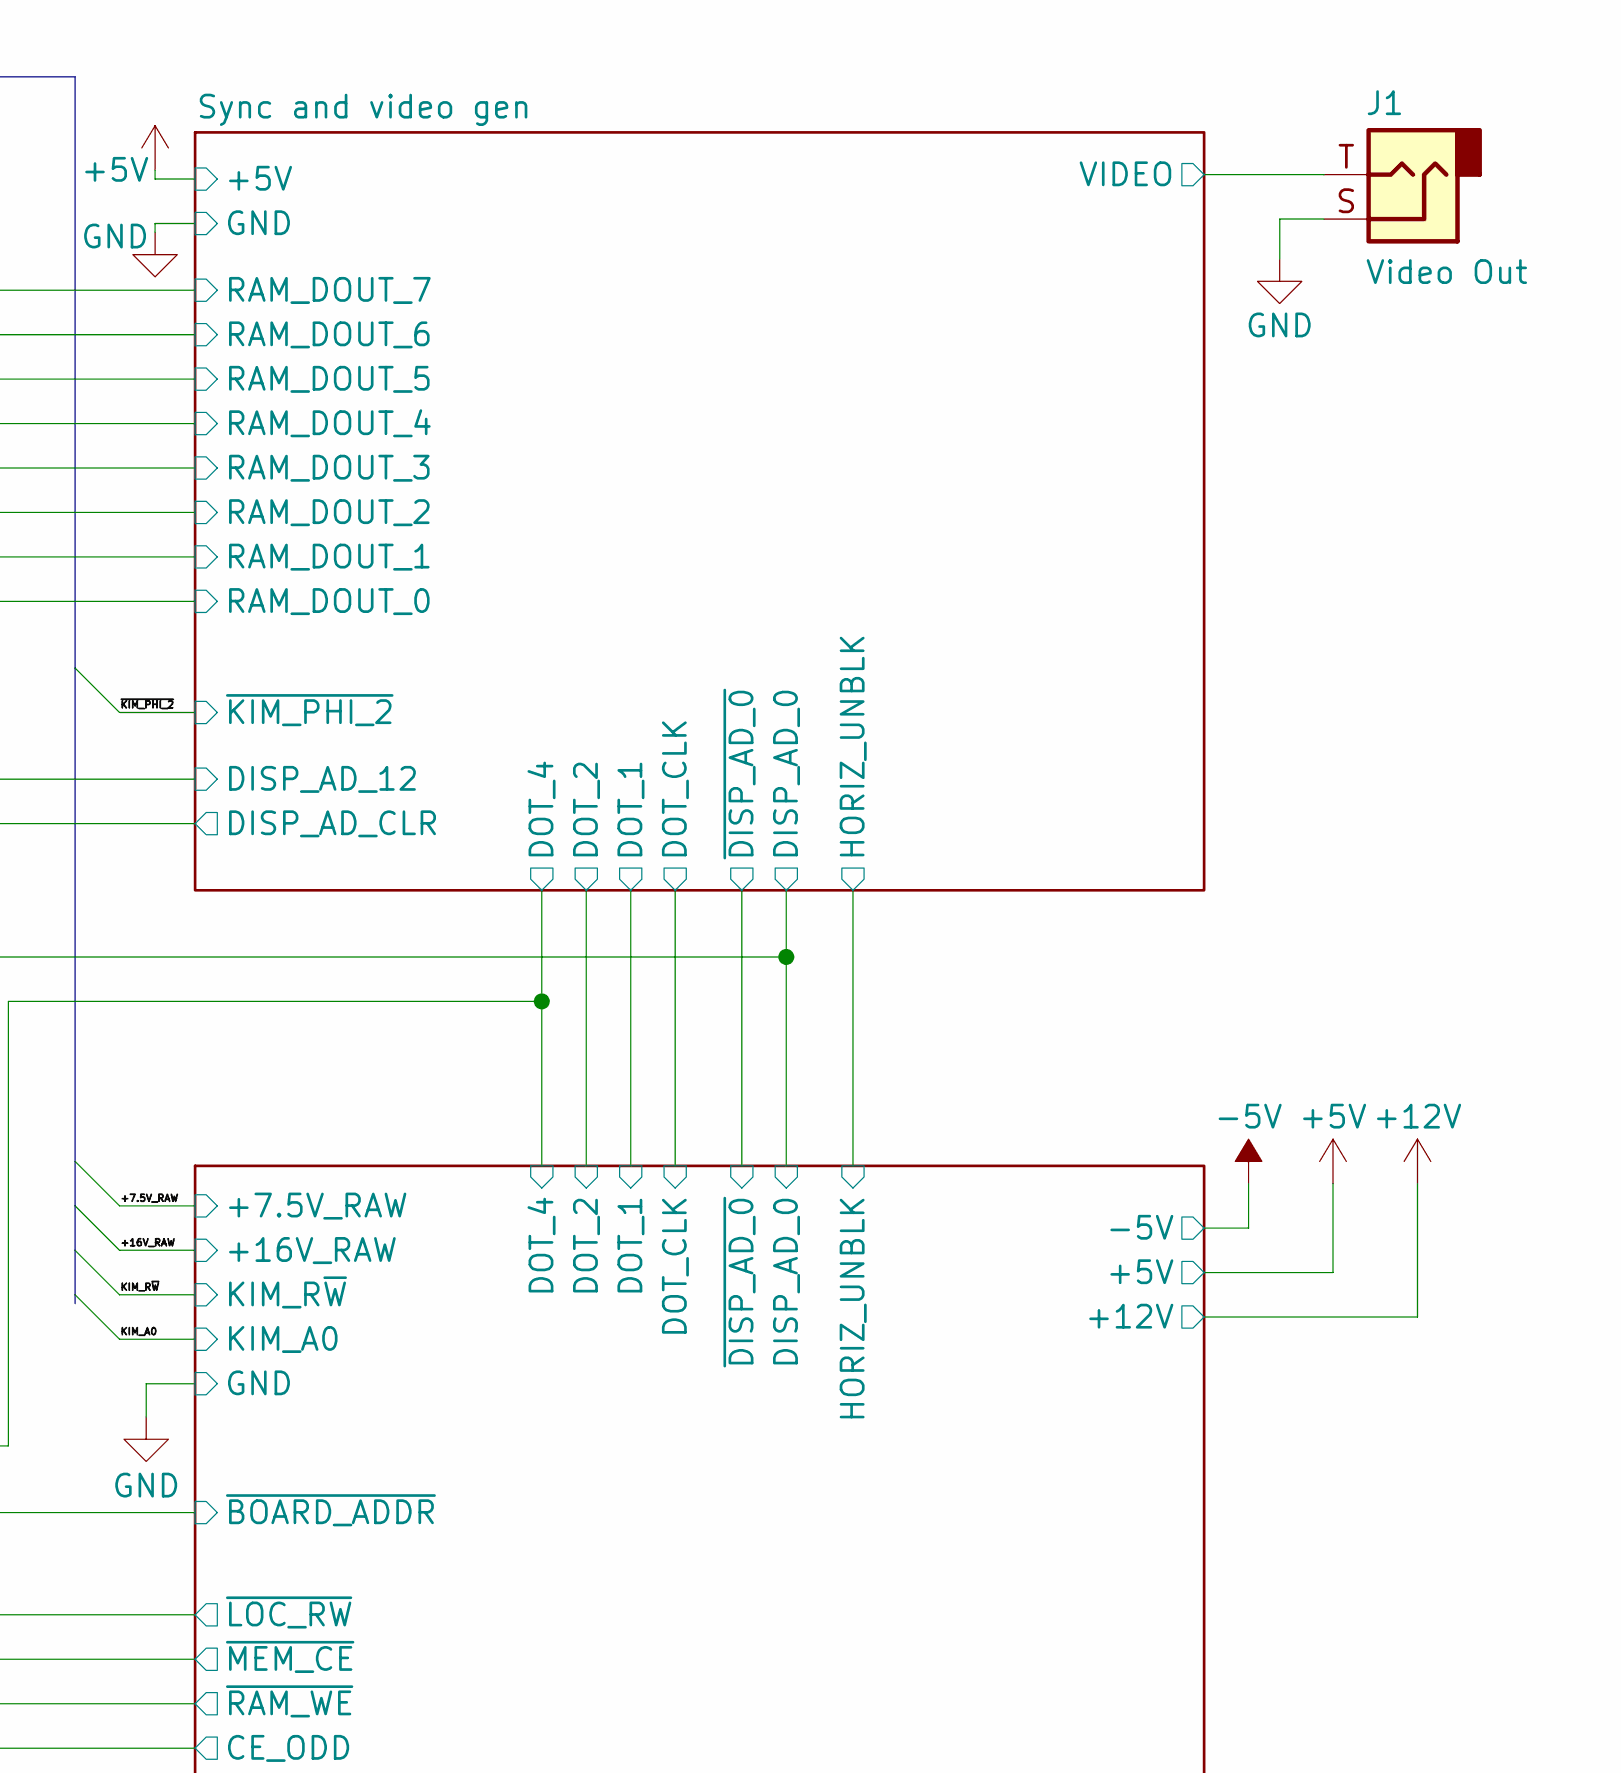
[picture p31: schematic k-1008-visable-memory.kicad_sch, part in row 1, column 3]

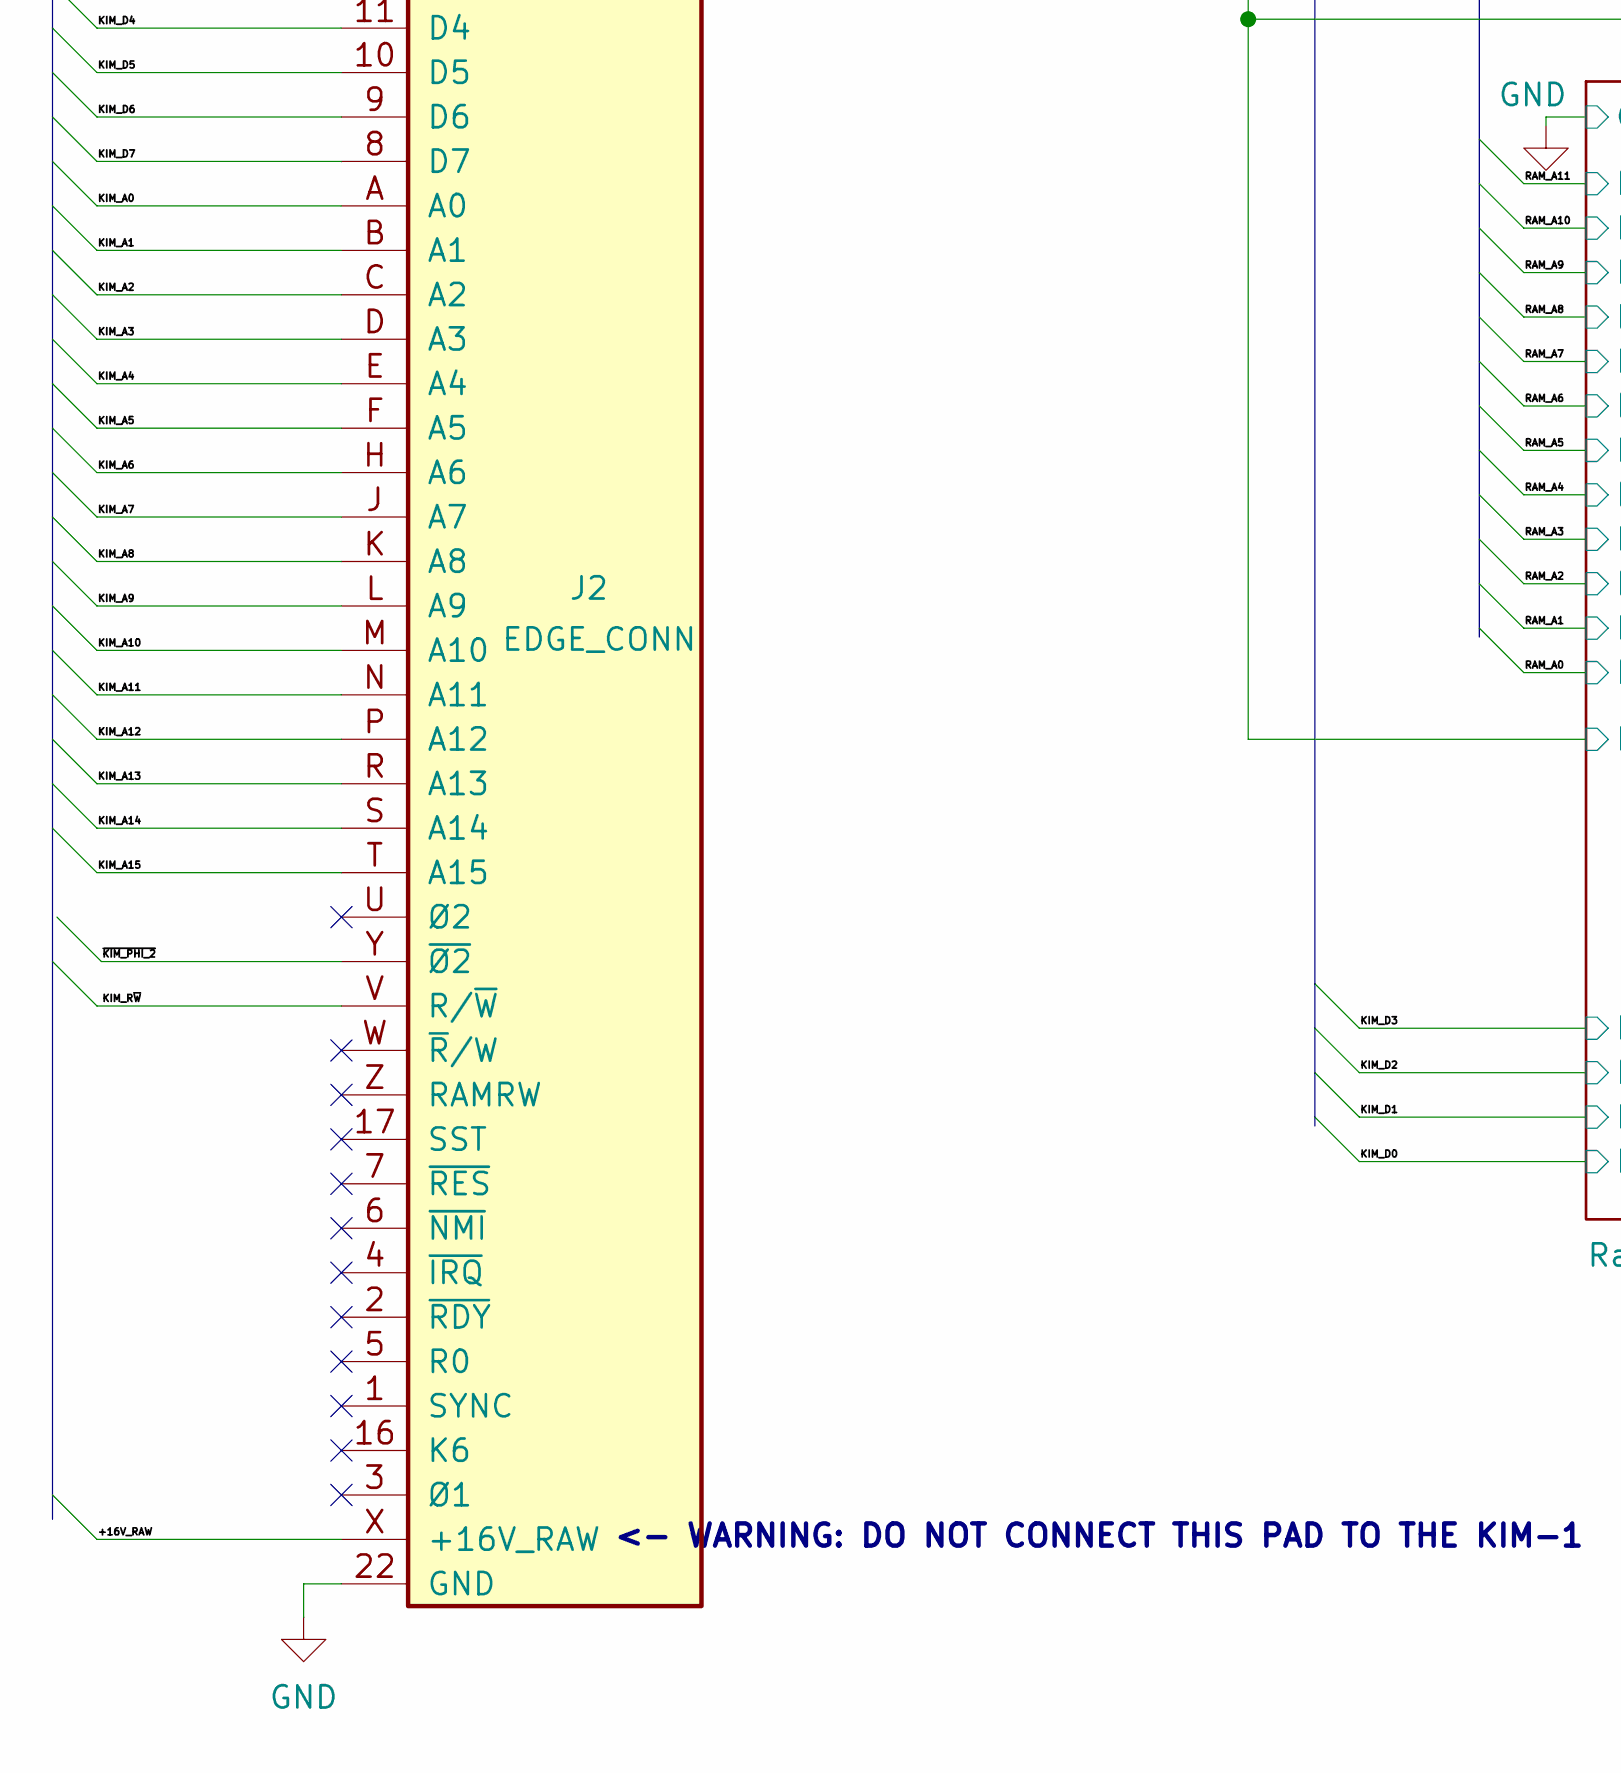
[picture p32: schematic k-1008-visable-memory.kicad_sch, part in row 2, column 1]

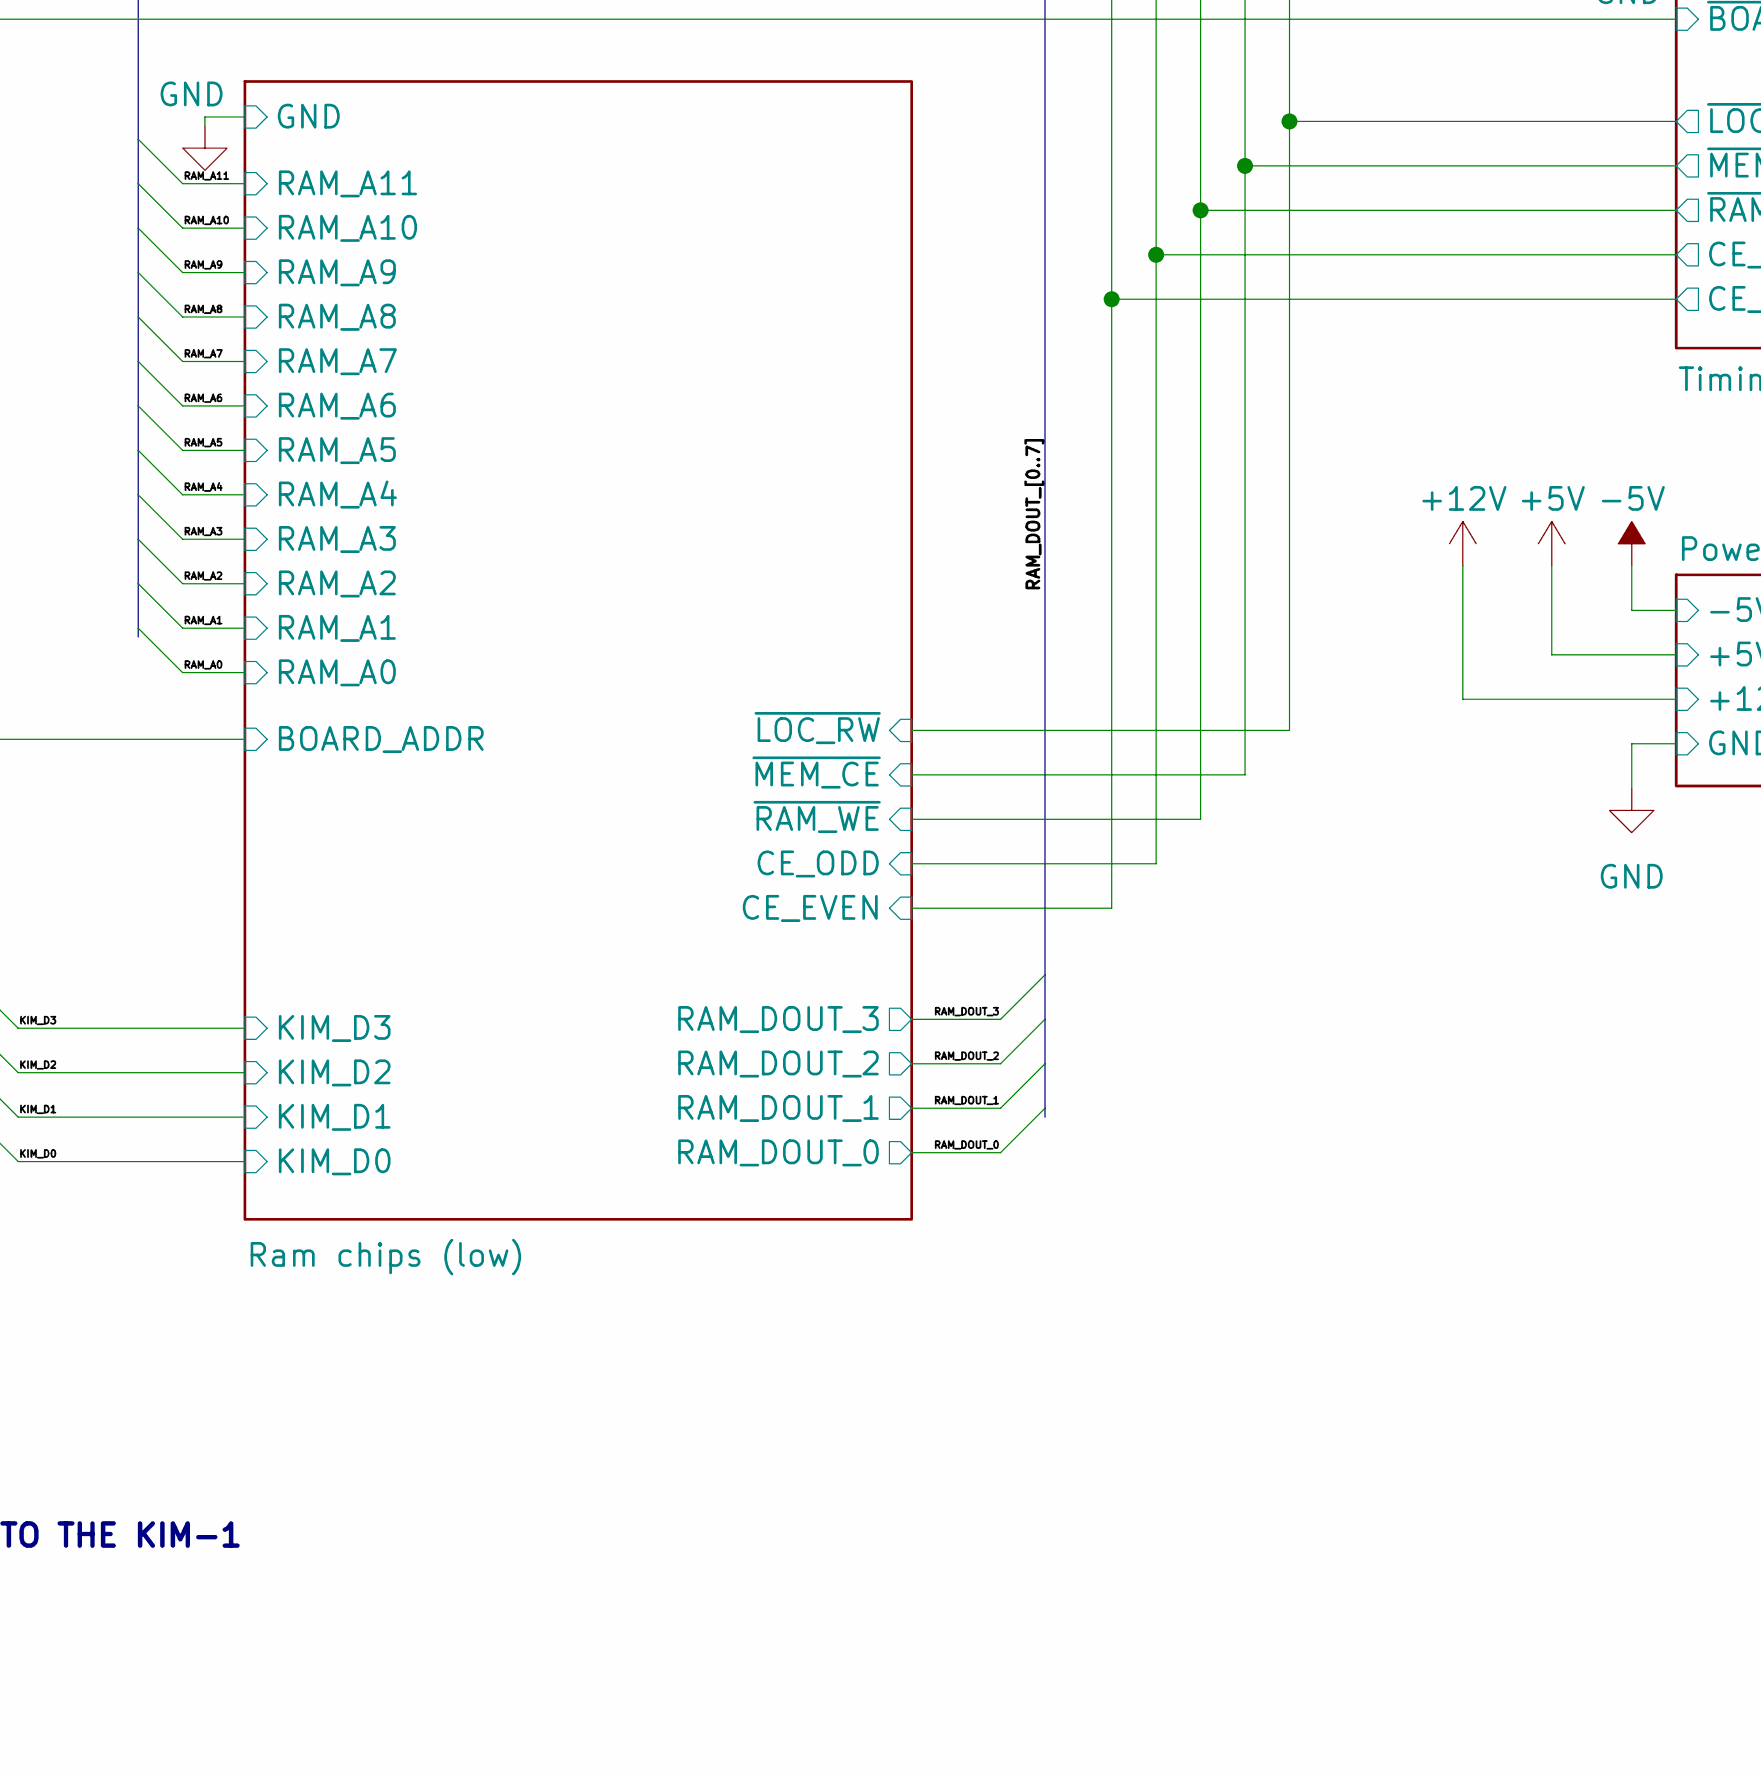
[picture p33: schematic k-1008-visable-memory.kicad_sch, part in row 2, column 2]

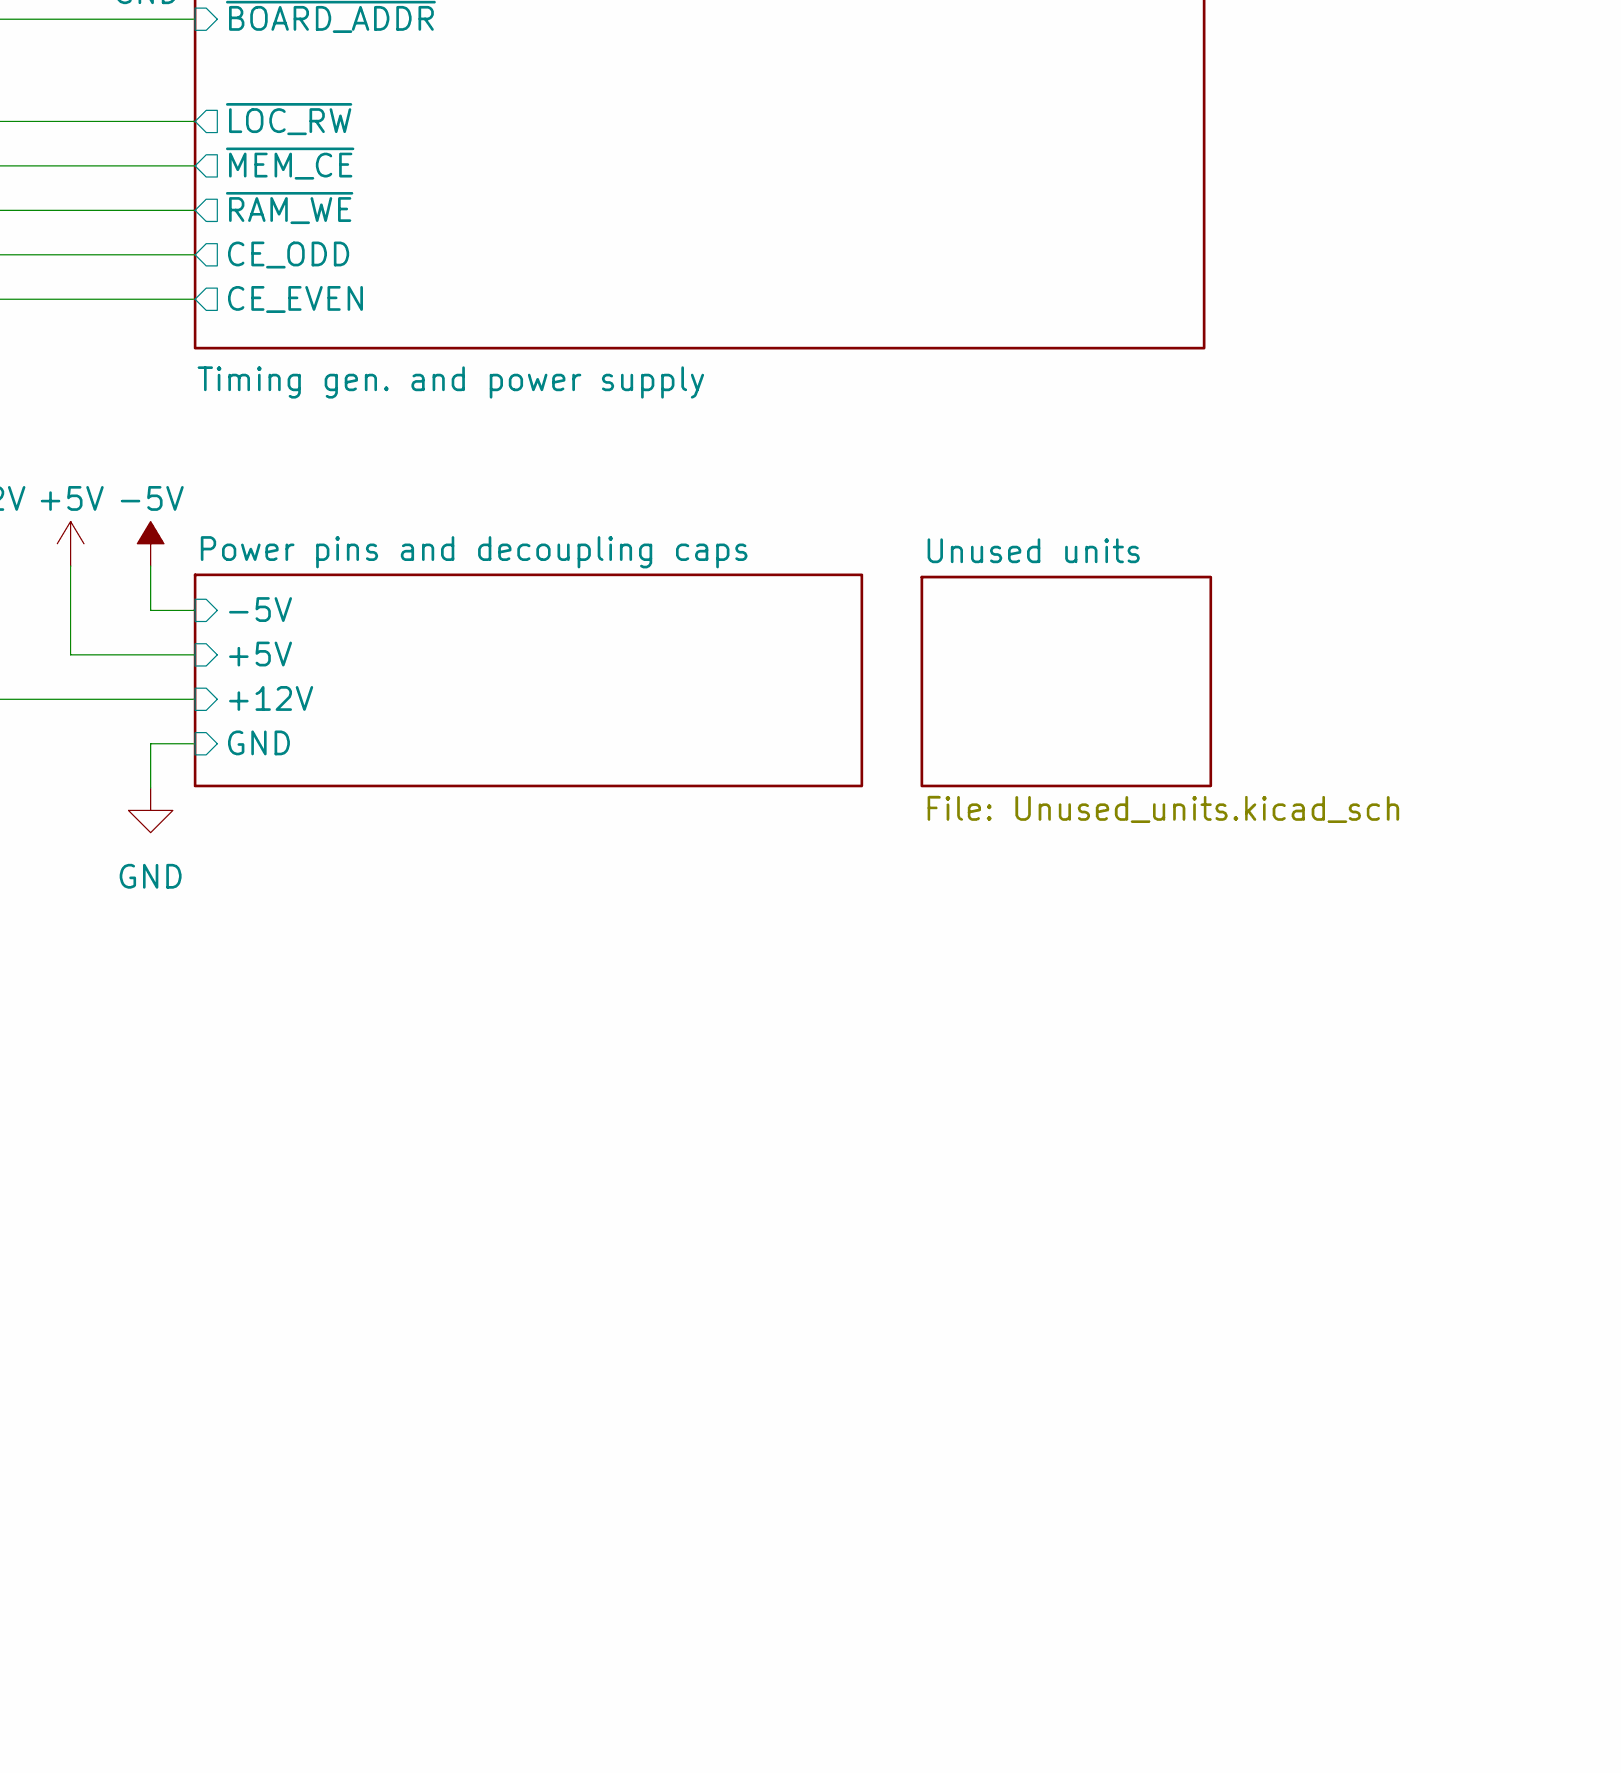
[picture p34: schematic k-1008-visable-memory.kicad_sch, part in row 2, column 3]

Parts:
J1: Video Out
J2: EDGE_CONN; KIM_CONN

Connections:
+7.5V_RAW: J2.18 (+7.5V_RAW)
+16V_RAW: J2.X (+16V_RAW)
GND: J1.S, J2.22 (GND)
KIM_A0: J2.A (A0)
KIM_A1: J2.B (A1)
KIM_A2: J2.C (A2)
KIM_A3: J2.D (A3)
KIM_A4: J2.E (A4)
KIM_A5: J2.F (A5)
KIM_A6: J2.H (A6)
KIM_A7: J2.J (A7)
KIM_A8: J2.K (A8)
KIM_A9: J2.L (A9)
KIM_A10: J2.M (A10)
KIM_A11: J2.N (A11)
KIM_A12: J2.P (A12)
KIM_A13: J2.R (A13)
KIM_A14: J2.S (A14)
KIM_A15: J2.T (A15)
KIM_D0: J2.15 (D0)
KIM_D1: J2.14 (D1)
KIM_D2: J2.13 (D2)
KIM_D3: J2.12 (D3)
KIM_D4: J2.11 (D4)
KIM_D5: J2.10 (D5)
KIM_D6: J2.9 (D6)
KIM_D7: J2.8 (D7)
KIM_R~W: J2.V (R/~W)
VIDEO: J1.T
~KIM_DECODE_ENABLE: J2.20 (~DECODE_ENABLE)
~KIM_PHI_2: J2.Y (~Ø2)
~KIM_VECTOR_FETCH: J2.19 (~VECTOR_FETCH)

Notes on the sheet:
<- WARNING: DO NOT CONNECT THIS PAD TO THE KIM-1
